bluepylons/Boston/graphics/3DP-LP/3DP-LP-gray-4.JPG

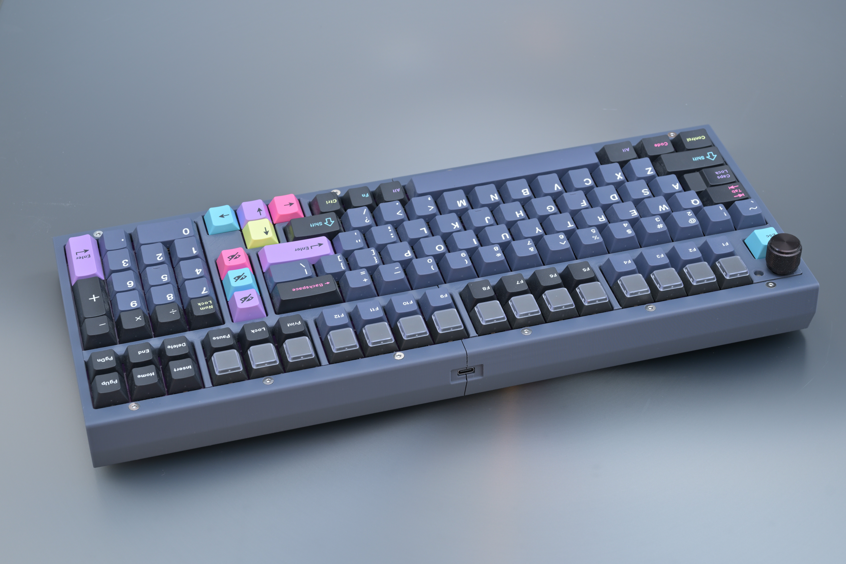
graphics/3DP-LP/3DP-LP-gray-4.JPG
