bluepylons/Boston/graphics/Metal-and-3DP-LP.JPG

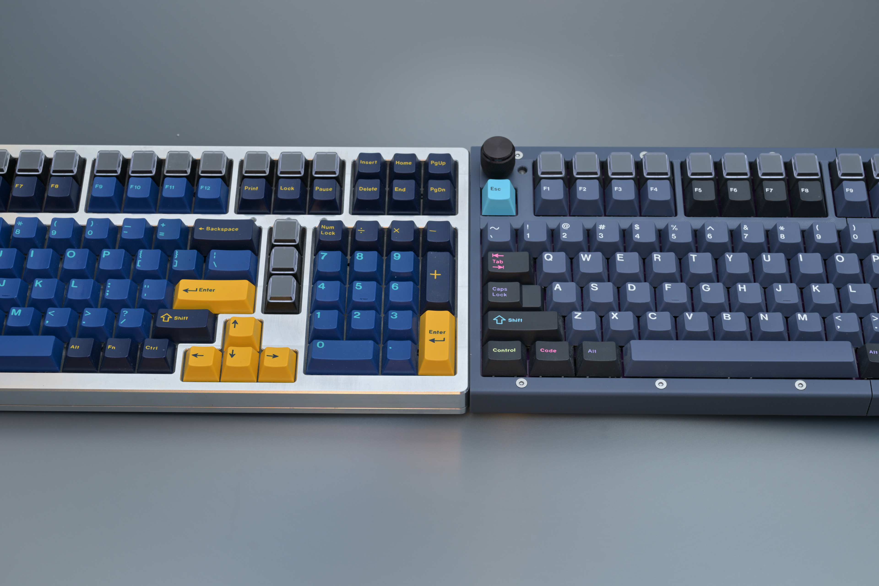
graphics/Metal-and-3DP-LP.JPG
