bluepylons/Boston/graphics/PCB-DB-bottom.png

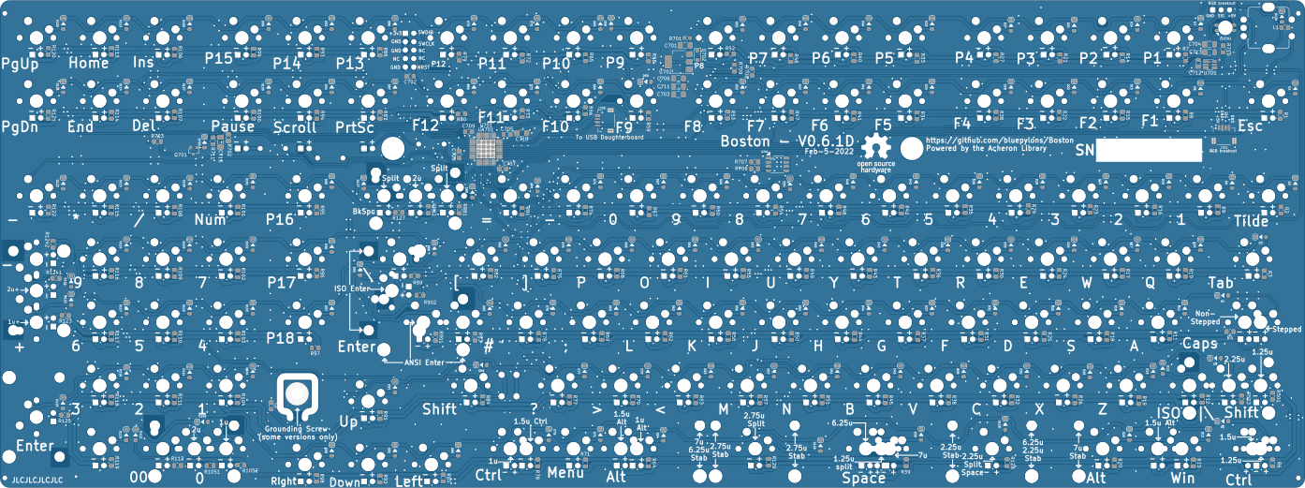
graphics/PCB-DB-bottom.png
