bluepylons/Boston/graphics/PCB-DB-top.png

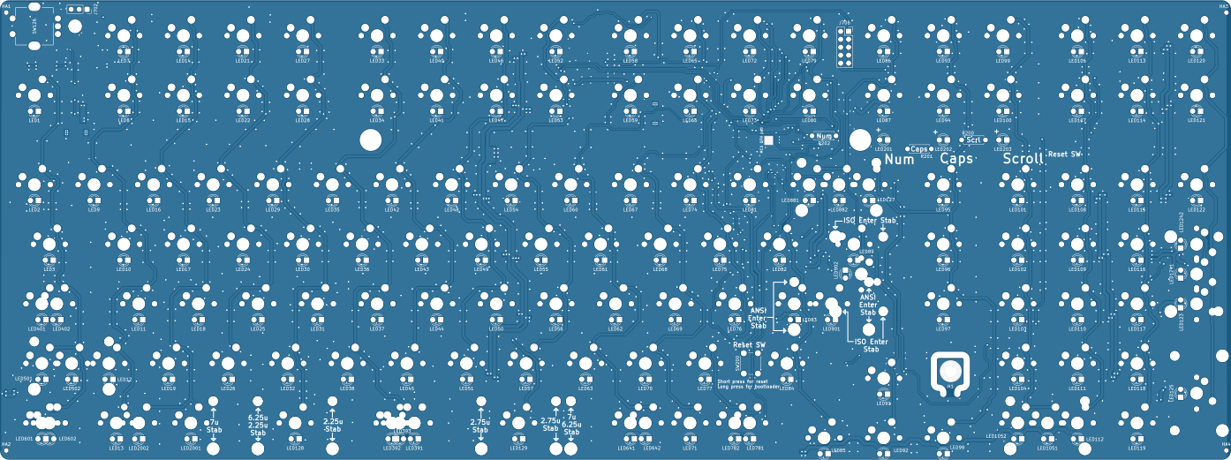
graphics/PCB-DB-top.png
