bluepylons/Boston/graphics/PCB-HS-bottom.png

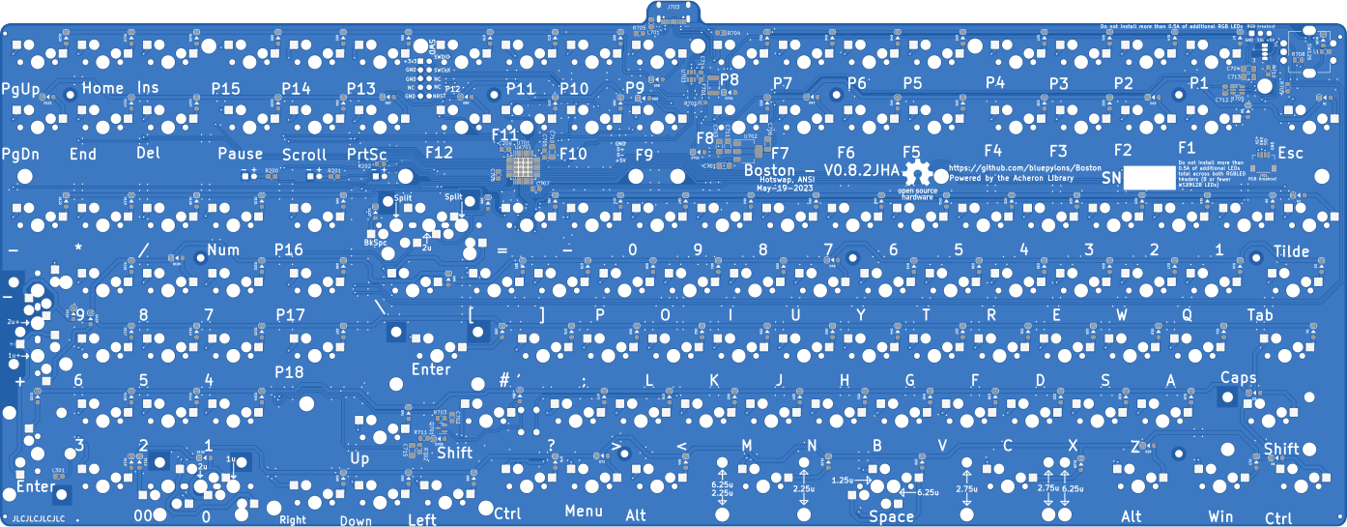
graphics/PCB-HS-bottom.png
