bluepylons/Boston/graphics/PCB-HS-DB-bottom.png

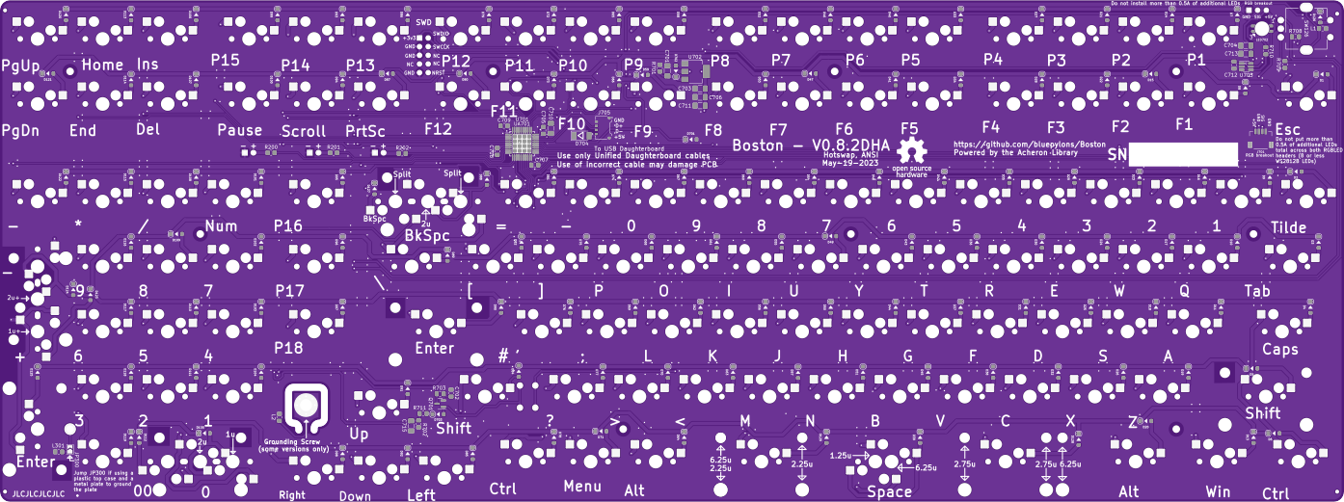
graphics/PCB-HS-DB-bottom.png
