bluepylons/Boston/graphics/PCB-HS-DB-top.png

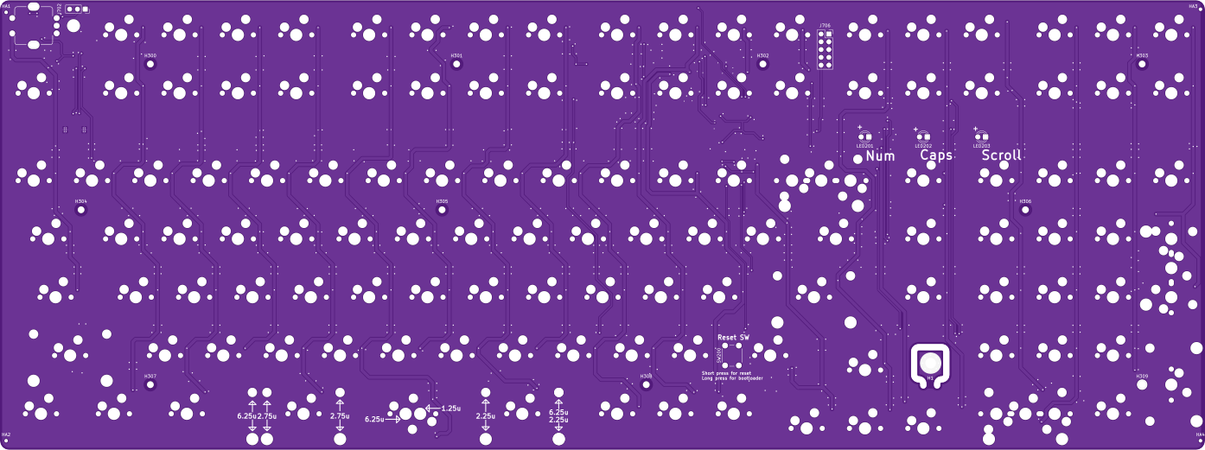
graphics/PCB-HS-DB-top.png
