bluepylons/Boston/graphics/PCB-HS-top.png

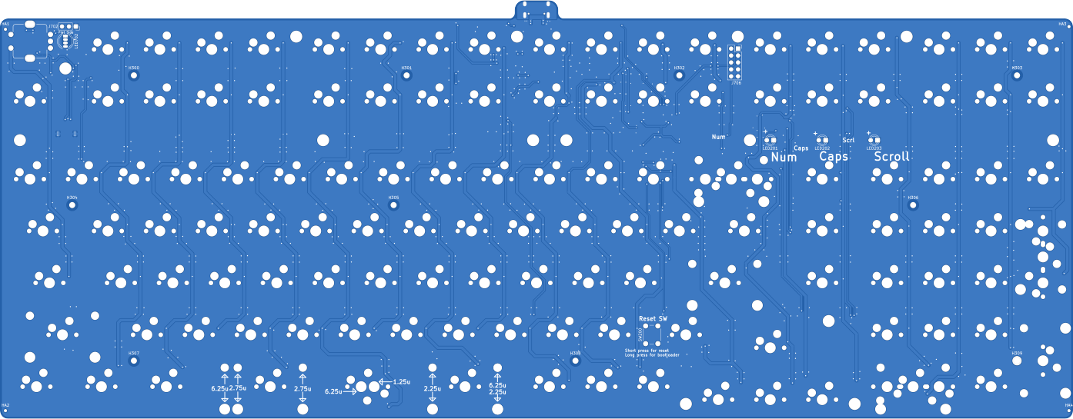
graphics/PCB-HS-top.png
