bluepylons/Boston/graphics/prototype_1_pic.JPG

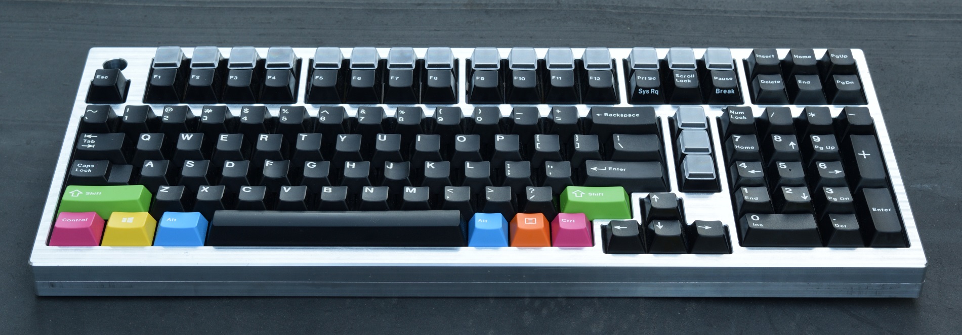
graphics/prototype_1_pic.JPG
