bluepylons/Boston/Boston - Current design/PCB/V0.8.2DHI/Manufacturing files/Elecrow SMT files/BostonV082DHI-Elecrow-files.xlsx

Sheet: PCB Specification
Your PCB Specification
PCB Quantity | 5pcs
Layer | 2layer
PCB Thickness | 1.6mm
Dimensions | 393.5 mm* 147 mm
Castellated Hole | No
PCB Color | Black
Surface Finish | HASL Lead Free
Copper Weight | 1oz
Text Color | White
Different Design | 1

Sheet: BOM
# | Reference | QTY | Value | Package | Manufacturer Part number | Description | SMD | THT | Original | Elecrow PN | Note
1 | C701, C703, C704, C706, C710, C711, C713, C715 | 8 | 10uF 50V X5R or X7R 20% | C1206 | Generic | MLCC Capacitor | 16 |  | N
2 | C702, C705, C707-C709, C712 | 6 | 100nF 50V X5R or X7R 20% | C0805 | Generic | MLCC Capacitor | 12 |  | N
3 | D1-D88, D90-D129, D703 | 129 | 1N4148W | SOD-123 | Generic | Signal Diode | 258 |  | N
4 | D701, D702 | 2 | RB060MM-60TR | SOD-123F | Rohm Semiconductor RB060MM-60TR | Schottky Diode | 4 |  | Y
5 | J705 | 1 | Molex Pico-Ezmate 78171-0004 | Molex Pico-Ezmate 78171-0004 | Molex Pico-Ezmate 78171-0004 | SMT connector | 6 |  | Y
6 | L1, L2, L301 | 3 | 60 ohm @ 100MHz | 0805 | CEC(Shenzhen Zhenhua Fu Elec) PB2012-600/1A0 (LCSC C2983032) | Ferrite bead | 6 |  | Y
7 | LED702 | 1 | SK6812mini-E | 3535_6028_3.2x2.8mm_Round | DONGGUAN OPSCO OPTOELECTRONICS CO., LTD SK6812Mini-E https://cdn-shop.adafruit.com/product-files/4960/4960_SK6812MINI-E_REV02_EN.pdf | SMT addressable RGBLED, reverse mount | 4 |  | Y
8 | Q701 | 1 | DTC123JKAT146 | SOT-23-3 | Rohm Semiconductor DTC123JKAT146 | Transistor | 3 |  | Y
9 | R200-R202 | 3 | 1K 5% | R0805 | Generic | 1K resistor | 6 |  | N
10 | R701 | 1 | 100K 5% | R0805 | Generic | 100K resistor | 2 |  | N
11 | R702 | 1 | 1M 1% | R0805 | Generic | 1M 1% resistor | 2 |  | N
12 | R708, R709 | 2 | 10K 5% | R0805 | Generic | 10K resistor | 4 |  | N
13 | R703, R710 | 2 | 100 5% | R0805 | Generic | 100 resistor | 4 |  | N
14 | R711 | 1 | 330K 1% | R0805 | Generic | 330K 1% resistor | 2 |  | N
15 | SW1-SW38,SW39-1,SW39-2,SW40-SW87,SW88-1,SW88-2,SW90-SW104,SW105-1,SW105-2,SW106-SW123,SW124-1,SW124-2,SW125-SW129 | 132 |  | Custom | Kailh CPG151101S11 | Keyboard switch socket | 264 |  | Y | CRP13070O | Black
16 | SW200 | 1 | SW_Push | Tact 6x6 5mm tall THT | Generic (e.g. Hongyuan Precision 1TS005A-2600-5001) | Tact switch |  | 4 | N |  | Solder to top side, not bottom!
17 | U701 | 1 | STM32F072CBx | LQFP-48 or QFN-48 | Any of the following: ST STM32F072CBU6 ST STM32F072CBU6TR ST STM32F072CBU7 ST STM32F072CBU7TR ST STM32F072CBT6 ST STM32F072CBT6TR ST STM32F072CBT7 ST STM32F072CBT7TR | Microcontroller | 49 |  | Y
18 | U702 | 1 | 3.3V LDO | SOT-223 | Any of the following: TI TLV1117LV33DCYR Diodes Inc AZ1117IH-3.3TRG1 | 3.3V LDO | 4 |  | Y
19 | U705 | 1 | 74LVC1T45 | SOT23-6 | Any of the following: TI SN74LVC1T45DBVR TI SN74LVC1T45DBVT Diodes Inc 74LVC1T45W6-7 | Level shifter | 6 |  | Y
20 | D704 | 1 | PMEG6030EVPX | SOD-128 | Nexperia PMEG6030EVPX | Schottky Diode | 2 |  | Y
 |  |  |  |  |  | Total | 638 | 4

Sheet: Position
Designator | Footprint | Center-X(mm) | Center-Y(mm) | Layer | Rotation
C701 | C_1206_3216Metric_Pad1.42x1.75mm_HandSolder | 253.1 | -48.725 | bottom | 90
C702 | C_0805_2012Metric_Pad1.15x1.40mm_HandSolder | 316.4 | -143.125 | bottom | 90
C703 | C_1206_3216Metric_Pad1.42x1.75mm_HandSolder | 243.5 | -53.925 | bottom | 0
C704 | C_1206_3216Metric_Pad1.42x1.75mm_HandSolder | 83.75 | -41.325 | bottom | 0
C705 | C_0805_2012Metric_Pad1.15x1.40mm_HandSolder | 289.4 | -66.164069 | bottom | -90
C706 | C_1206_3216Metric_Pad1.42x1.75mm_HandSolder | 243.5 | -56.425 | bottom | 0
C707 | C_0805_2012Metric_Pad1.15x1.40mm_HandSolder | 291.9 | -76.325 | bottom | 0
C708 | C_0805_2012Metric_Pad1.15x1.40mm_HandSolder | 302.9 | -72.325 | bottom | 90
C709 | C_0805_2012Metric_Pad1.15x1.40mm_HandSolder | 300.890625 | -64.821875 | bottom | 180
C710 | C_1206_3216Metric_Pad1.42x1.75mm_HandSolder | 287.2 | -65.568756 | bottom | -90
C711 | C_1206_3216Metric_Pad1.42x1.75mm_HandSolder | 243.5 | -58.925 | bottom | 0
C712 | C_0805_2012Metric_Pad1.15x1.40mm_HandSolder | 87.2 | -47.025 | bottom | -90
C713 | C_1206_3216Metric_Pad1.42x1.75mm_HandSolder | 83.725 | -43.725 | bottom | 0
C715 | C_1206_3216Metric_Pad1.42x1.75mm_HandSolder | 328.1 | -152.725 | bottom | -90
D1 | D_SOD-123 | 61.5 | -49.725 | bottom | 180
D2 | D_SOD-123 | 69.1 | -78.225 | bottom | 180
D3 | D_SOD-123 | 62.428125 | -98.90625 | bottom | -90
D4 | D_SOD-123 | 64.809375 | -117.95625 | bottom | -90
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
SW97 | MX100H | 356.5125 | -125.1 | bottom | 180
SW98 | MX100H | 356.5125 | -167.9625 | bottom | 180
SW99 | MX100H | 375.5625 | -39.375 | bottom | 180
SW100 | MX100H | 375.5625 | -58.425 | bottom | 180
SW101 | MX100H | 380.325 | -87 | bottom | 180
SW102 | MX100H | 380.325 | -106.05 | bottom | 180
SW103 | MX100H | 380.325 | -125.1 | bottom | 180
SW104 | MX100H | 380.325 | -144.15 | bottom | 180
SW105-1 | MX200H | 389.85 | -163.2 | bottom | 180
SW105-2 | MX100H | 380.325 | -163.2 | bottom | 0
SW106 | MX100H | 399.375 | -39.375 | bottom | 180
SW107 | MX100H | 399.375 | -58.425 | bottom | 180
SW108 | MX100H | 399.375 | -87 | bottom | 180
SW109 | MX100H | 399.375 | -106.05 | bottom | 180
SW110 | MX100H | 399.375 | -125.1 | bottom | 180
SW111 | MX100H | 399.375 | -144.15 | bottom | 180
SW112 | MX100H | 399.375 | -163.2 | bottom | 0
SW113 | MX100H | 418.425 | -39.375 | bottom | 180
SW114 | MX100H | 418.425 | -58.425 | bottom | 180
SW115 | MX100H | 418.425 | -87 | bottom | 180
SW116 | MX100H | 418.425 | -106.05 | bottom | 180
SW117 | MX100H | 418.425 | -125.1 | bottom | 180
SW118 | MX100H | 418.425 | -144.15 | bottom | 180
SW119 | MX100H | 418.425 | -163.2 | bottom | 180
SW120 | MX100H | 437.475 | -39.375 | bottom | 180
SW121 | MX100H | 437.475 | -58.425 | bottom | 180
SW122 | MX100H | 437.475 | -87 | bottom | 180
SW123 | MX100H | 437.475 | -125.1 | bottom | -90
SW124-1 | MX200H | 437.475 | -115.575 | bottom | 90
SW124-2 | MX100H | 437.475 | -106.05 | bottom | -90
SW125 | MX200HR | 437.475 | -153.675 | bottom | 90
SW126 | ALPS_EC11E | 66 | -36.375 | bottom | -90
SW127 | MX100H | 332.7 | -87 | bottom | 0
SW128 | MX275H | 154.10625 | -163.2 | bottom | 180
SW129 | MX225H | 225.54375 | -163.2 | bottom | 180
U701 | LQFP-48_7x7mm_P0.5mm | 295.650625 | -70.066875 | bottom | 180
U702 | SOT-223-3_TabPin2 | 244.8 | -48.925 | bottom | 180
U705 | SOT-23-6_Handsoldering | 83.62125 | -47.47125 | bottom | 180
