bluepylons/Boston/graphics/Assembly-guide-3DP/Parts-FR4-rubber-feet-holder.jpg

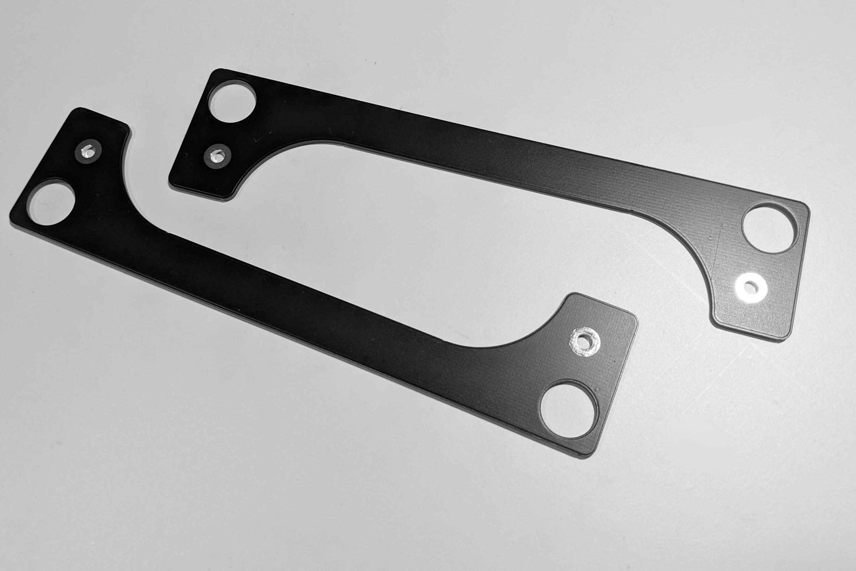
graphics/Assembly-guide-3DP/Parts-FR4-rubber-feet-holder.jpg
