bluepylons/Boston/graphics/Assembly-guide-3DP/Parts-rubber-feet.jpg

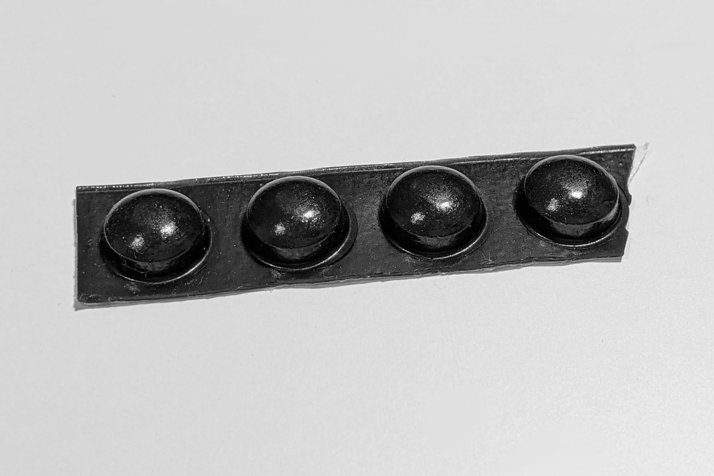
graphics/Assembly-guide-3DP/Parts-rubber-feet.jpg
