bluepylons/Boston/Experimental designs/Lower profile 3DP/Right-key-separator-revised.stp

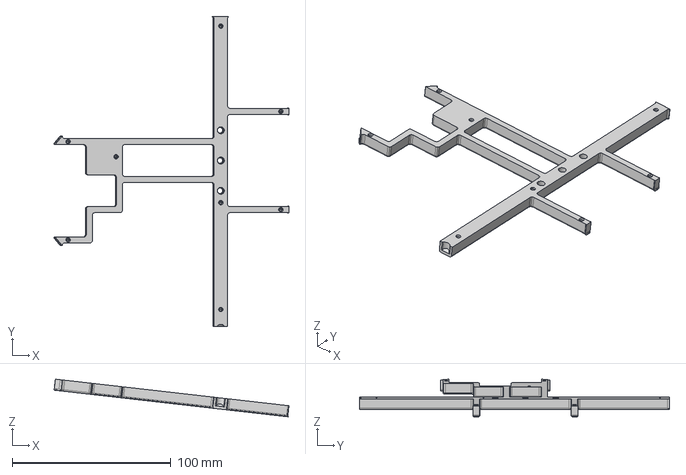
[picture p52: CAD file, 2026-01-18]
Experimental designs/Lower profile 3DP/Right-key-separator-revised.stp
148.0 x 195.4 x 23.8 mm
