bluepylons/Boston/Boston - Current design/3D printed version/STLs/RGBLED-LED-spacer.stl

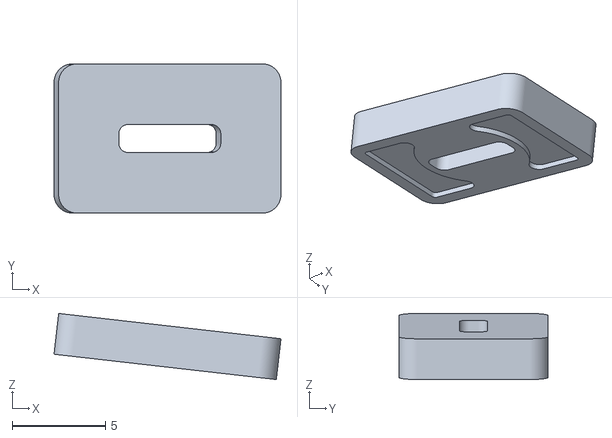
[picture p53: CAD file, 2023-04-24]
Boston - Current design/3D printed version/STLs/RGBLED-LED-spacer.stl
12.2 x 8.00 x 3.54
