bluepylons/Boston/Boston - Current design/CNC version/Case/STEP/Boston-top.stp

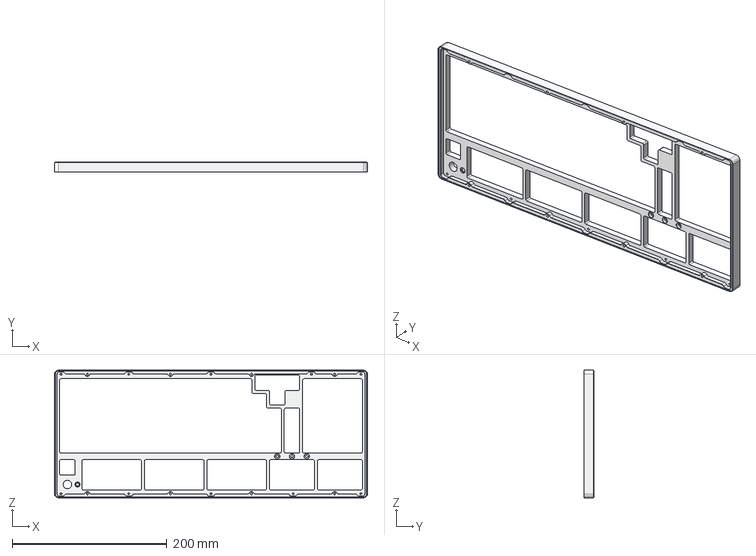
[picture p54: CAD file, 2023-04-24]
Boston - Current design/CNC version/Case/STEP/Boston-top.stp
405.0 x 13.5 x 165.0 mm
