bluepylons/Boston/Experimental designs/Lower profile 3DP/Lower-profile-right-half.stp

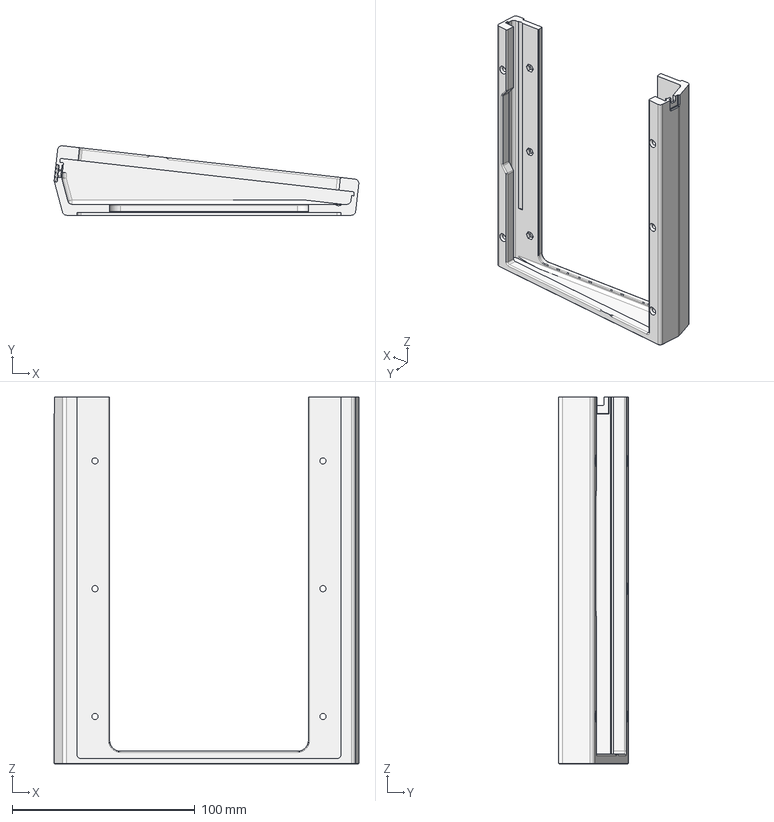
[picture p55: CAD file, 2026-01-18]
Experimental designs/Lower profile 3DP/Lower-profile-right-half.stp
166.9 x 38.1 x 201.0 mm
