bluepylons/Boston/Boston - Current design/3D printed version/STLs/Right-half.stl

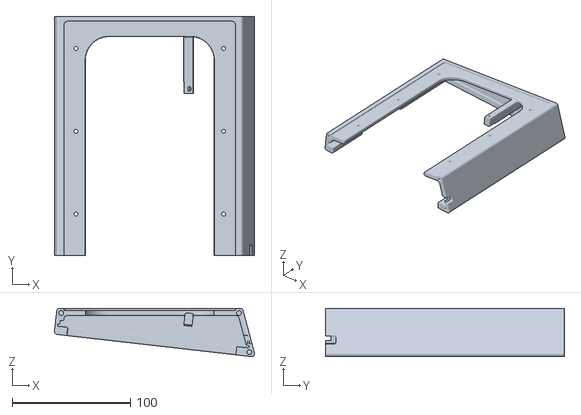
[picture p57: CAD file, 2023-04-24]
Boston - Current design/3D printed version/STLs/Right-half.stl
169.3 x 202.0 x 40.8
