bluepylons/Boston/Boston - Current design/3D printed version/STLs/3mm-LED-spacer.stl

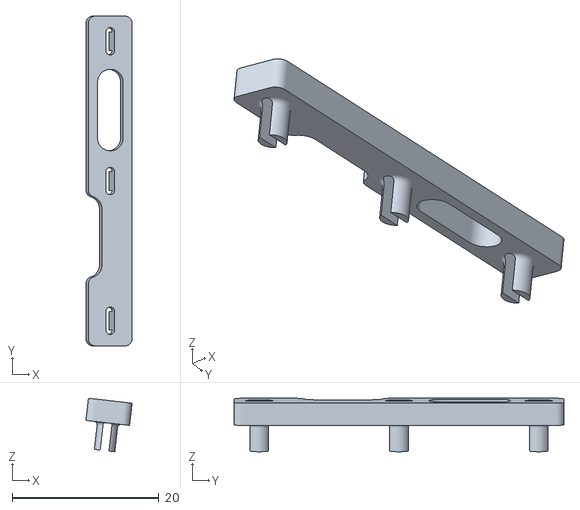
[picture p58: CAD file, 2023-04-24]
Boston - Current design/3D printed version/STLs/3mm-LED-spacer.stl
6.31 x 45.0 x 7.30
