bluepylons/Boston/Boston - Current design/3D printed version/Bottom (without reset hole)/Artwork files (courtesy OpenStreetMap)/boston-streets-8.png

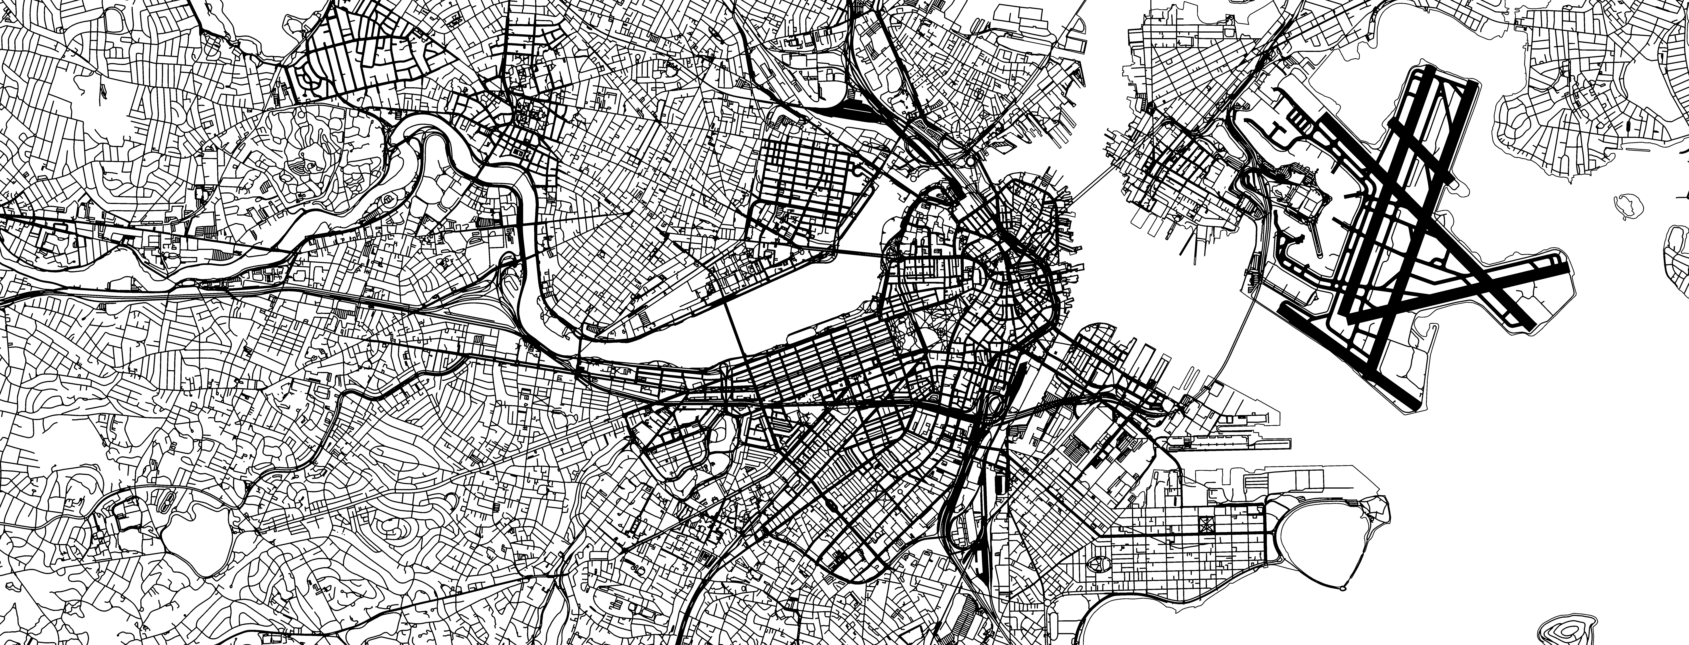
Boston - Current design/3D printed version/Bottom (without reset hole)/Artwork files (courtesy OpenStreetMap)/boston-streets-8.png
