bluepylons/Boston/Boston - Current design/CNC version/Case/Manufacturing drawings/Boston-bottom-alternate-AS-MACHINED-milling-instructions.png

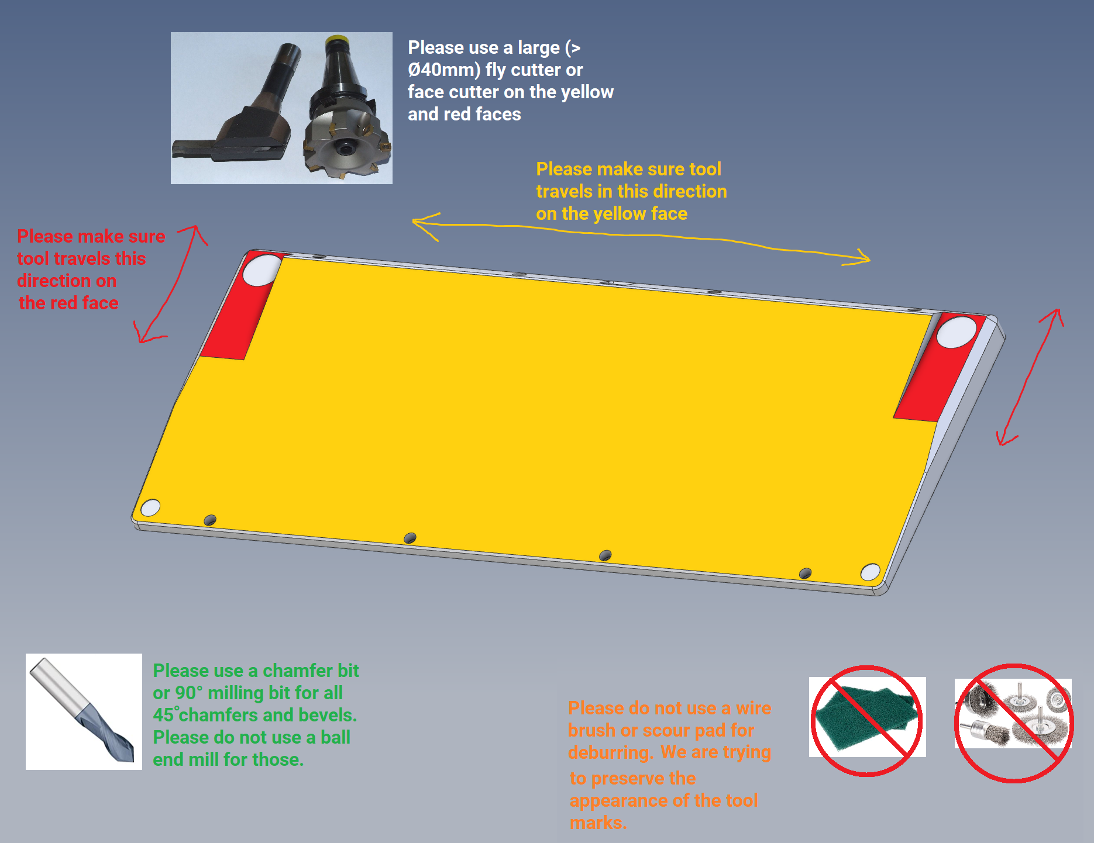
Boston - Current design/CNC version/Case/Manufacturing drawings/Boston-bottom-alternate-AS-MACHINED-milling-instructions.png
