bluepylons/Boston/Boston - Current design/CNC version/Case/Manufacturing drawings/Boston-bottom-AS-MACHINED-milling-instructions.png

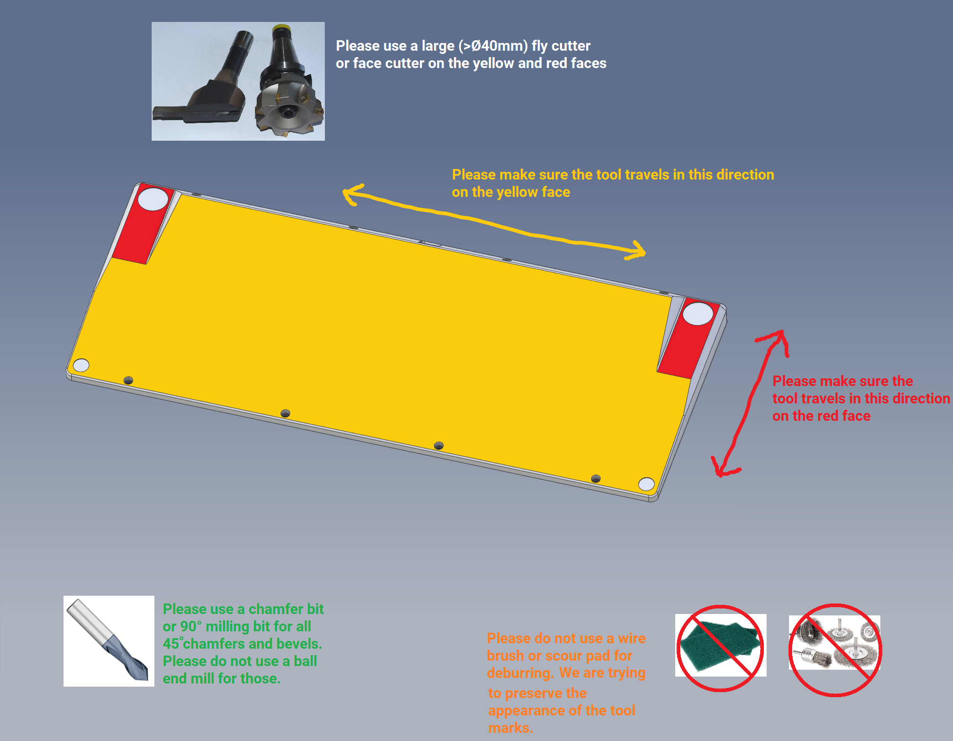
Boston - Current design/CNC version/Case/Manufacturing drawings/Boston-bottom-AS-MACHINED-milling-instructions.png
