bluepylons/Boston/Boston - Current design/PCB/V0.8.2DHA/Manufacturing files/Elecrow SMT files/SW200-instructions.png

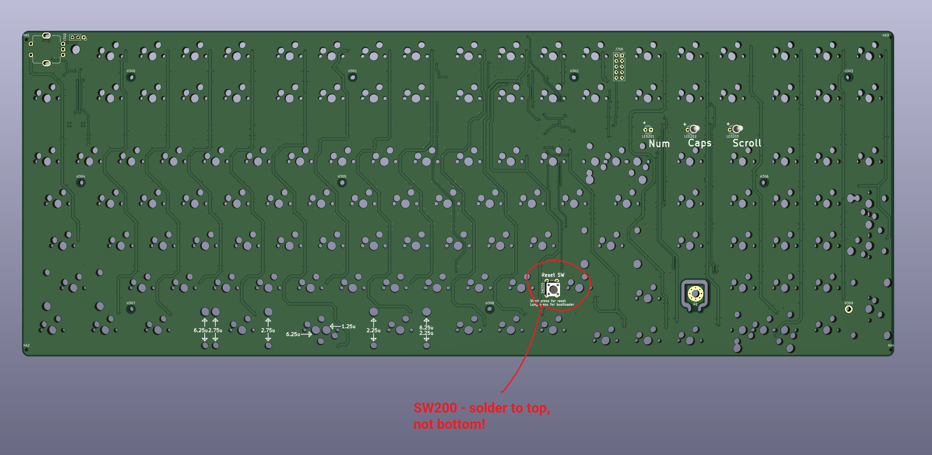
Boston - Current design/PCB/V0.8.2DHA/Manufacturing files/Elecrow SMT files/SW200-instructions.png
