bluepylons/Boston/Boston - Current design/PCB/V0.8.2DHI/Manufacturing files/Elecrow SMT files/SW200.png

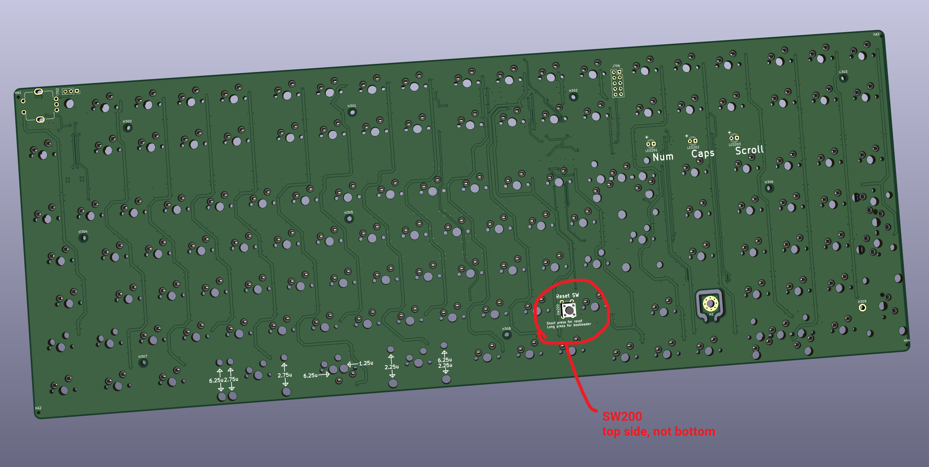
Boston - Current design/PCB/V0.8.2DHI/Manufacturing files/Elecrow SMT files/SW200.png
