bluepylons/Boston/Boston - Current design/PCB/V0.8.2JHA/Manufacturing files/Elecrow SMT files/SW200+LED702-instructions.png

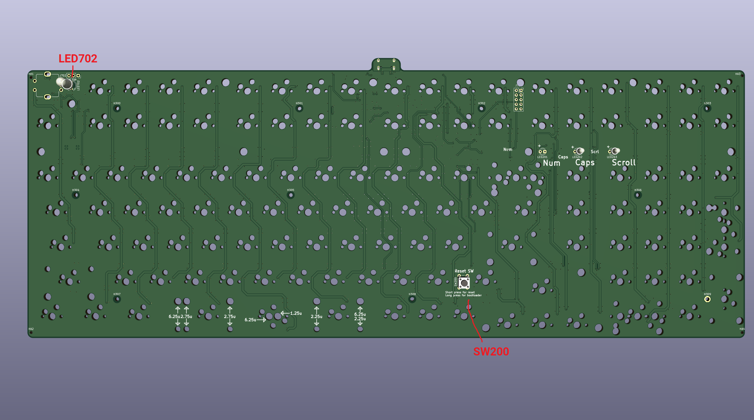
Boston - Current design/PCB/V0.8.2JHA/Manufacturing files/Elecrow SMT files/SW200+LED702-instructions.png
