bluepylons/Boston/Boston - Current design/PCB/V0.8D/Manufacturing files/Elecrow SMT files/SW200-instructions.png

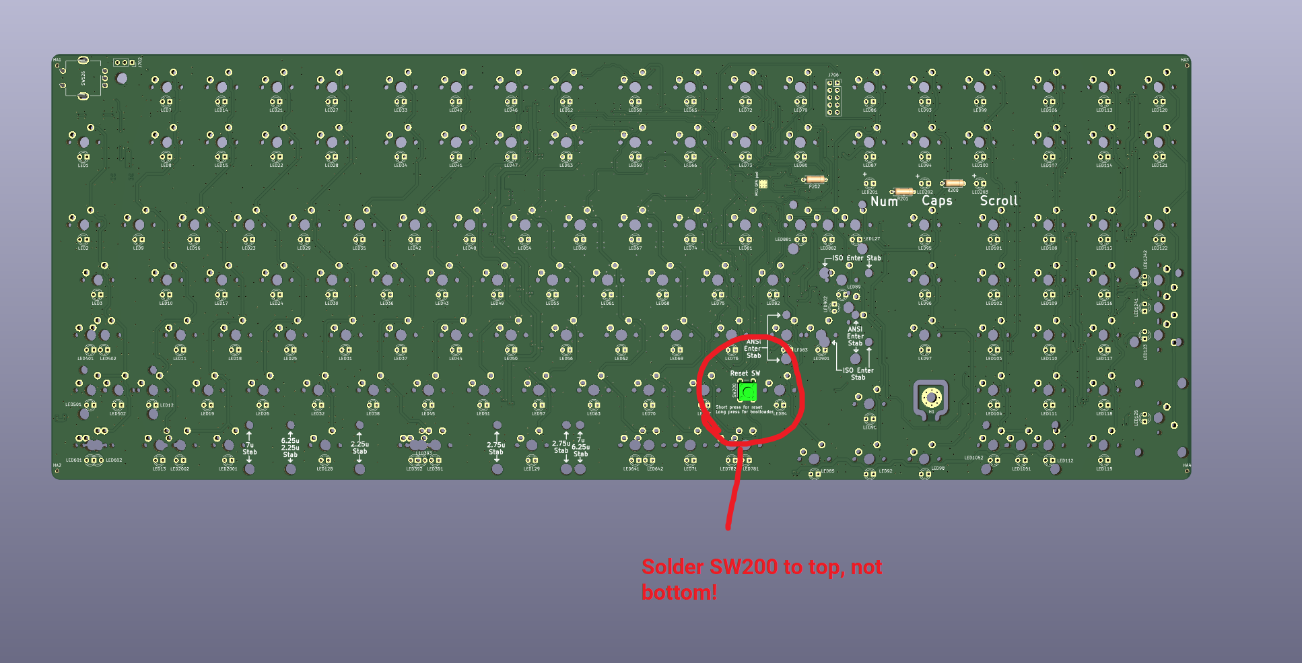
Boston - Current design/PCB/V0.8D/Manufacturing files/Elecrow SMT files/SW200-instructions.png
