bluepylons/Boston/Boston - Current design/PCB/V0.8J/Manufacturing files/Elecrow SMT files/SW200+LED702-instructions.png

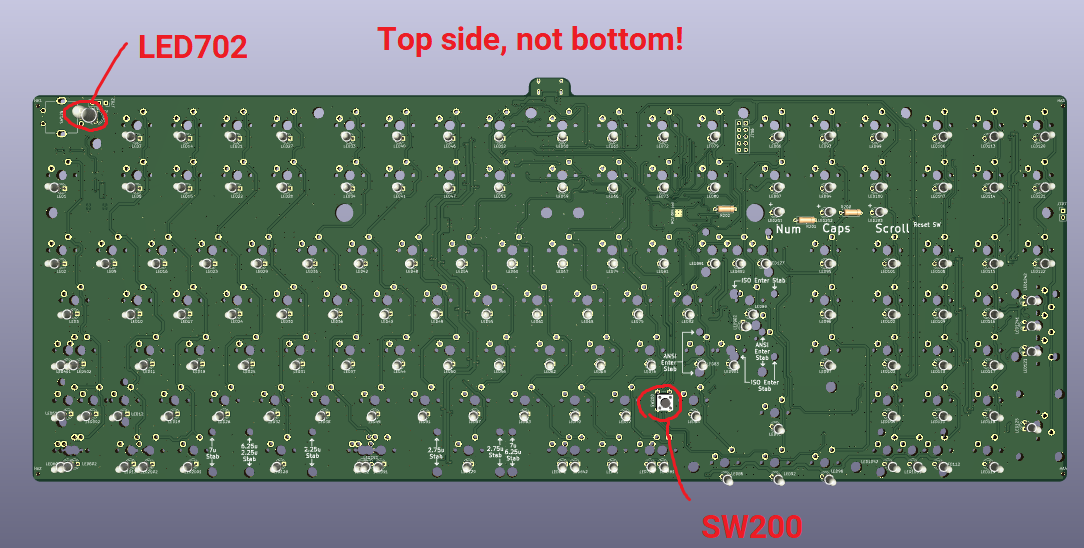
Boston - Current design/PCB/V0.8J/Manufacturing files/Elecrow SMT files/SW200+LED702-instructions.png
