bluepylons/Boston/graphics/3DP-LP/3DP-LP-half-assembled2.JPG

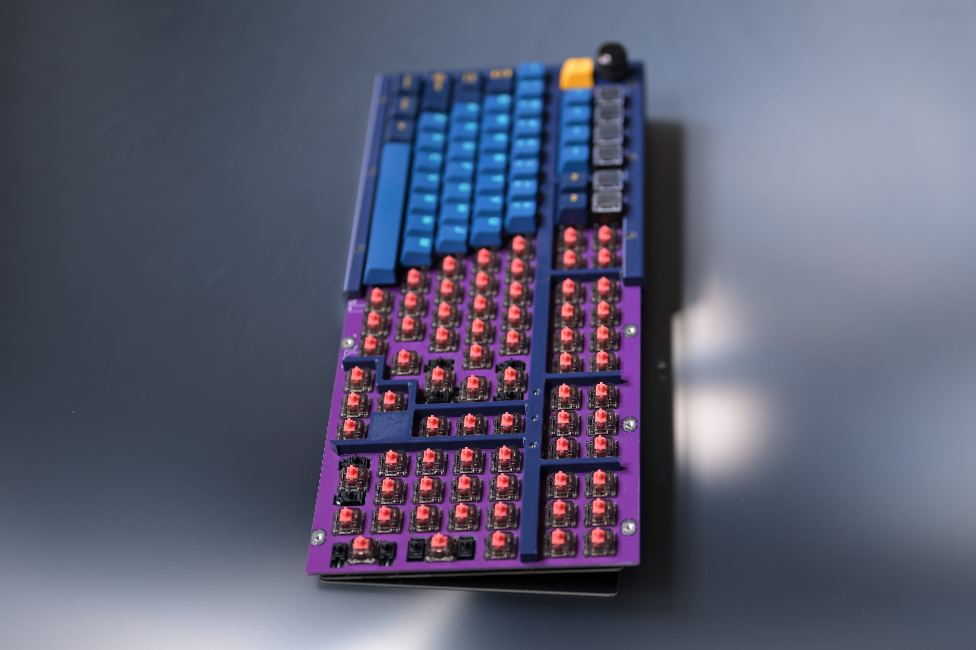
graphics/3DP-LP/3DP-LP-half-assembled2.JPG
