bluepylons/Boston/graphics/3DP-LP/3DP-LP-half-assembled.JPG

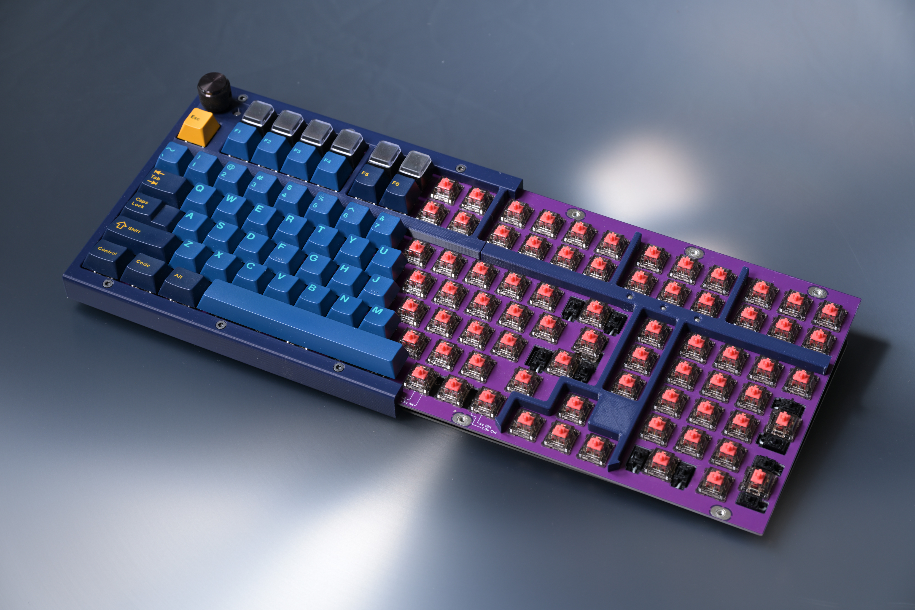
graphics/3DP-LP/3DP-LP-half-assembled.JPG
