bluepylons/Boston/graphics/Assembly-guide-3DP/PCB-LED-polarity.jpg

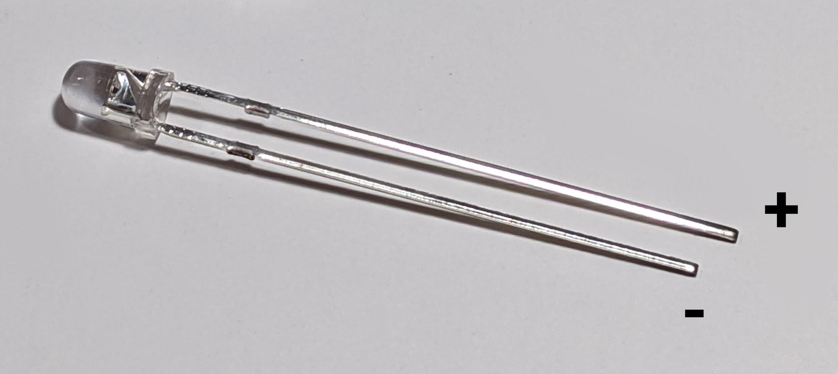
graphics/Assembly-guide-3DP/PCB-LED-polarity.jpg
