bluepylons/Boston/Boston - Current design/PCB/Older PCB revisions/V0.8.1JHA/Boston-keyboard-V081JHA.pdf

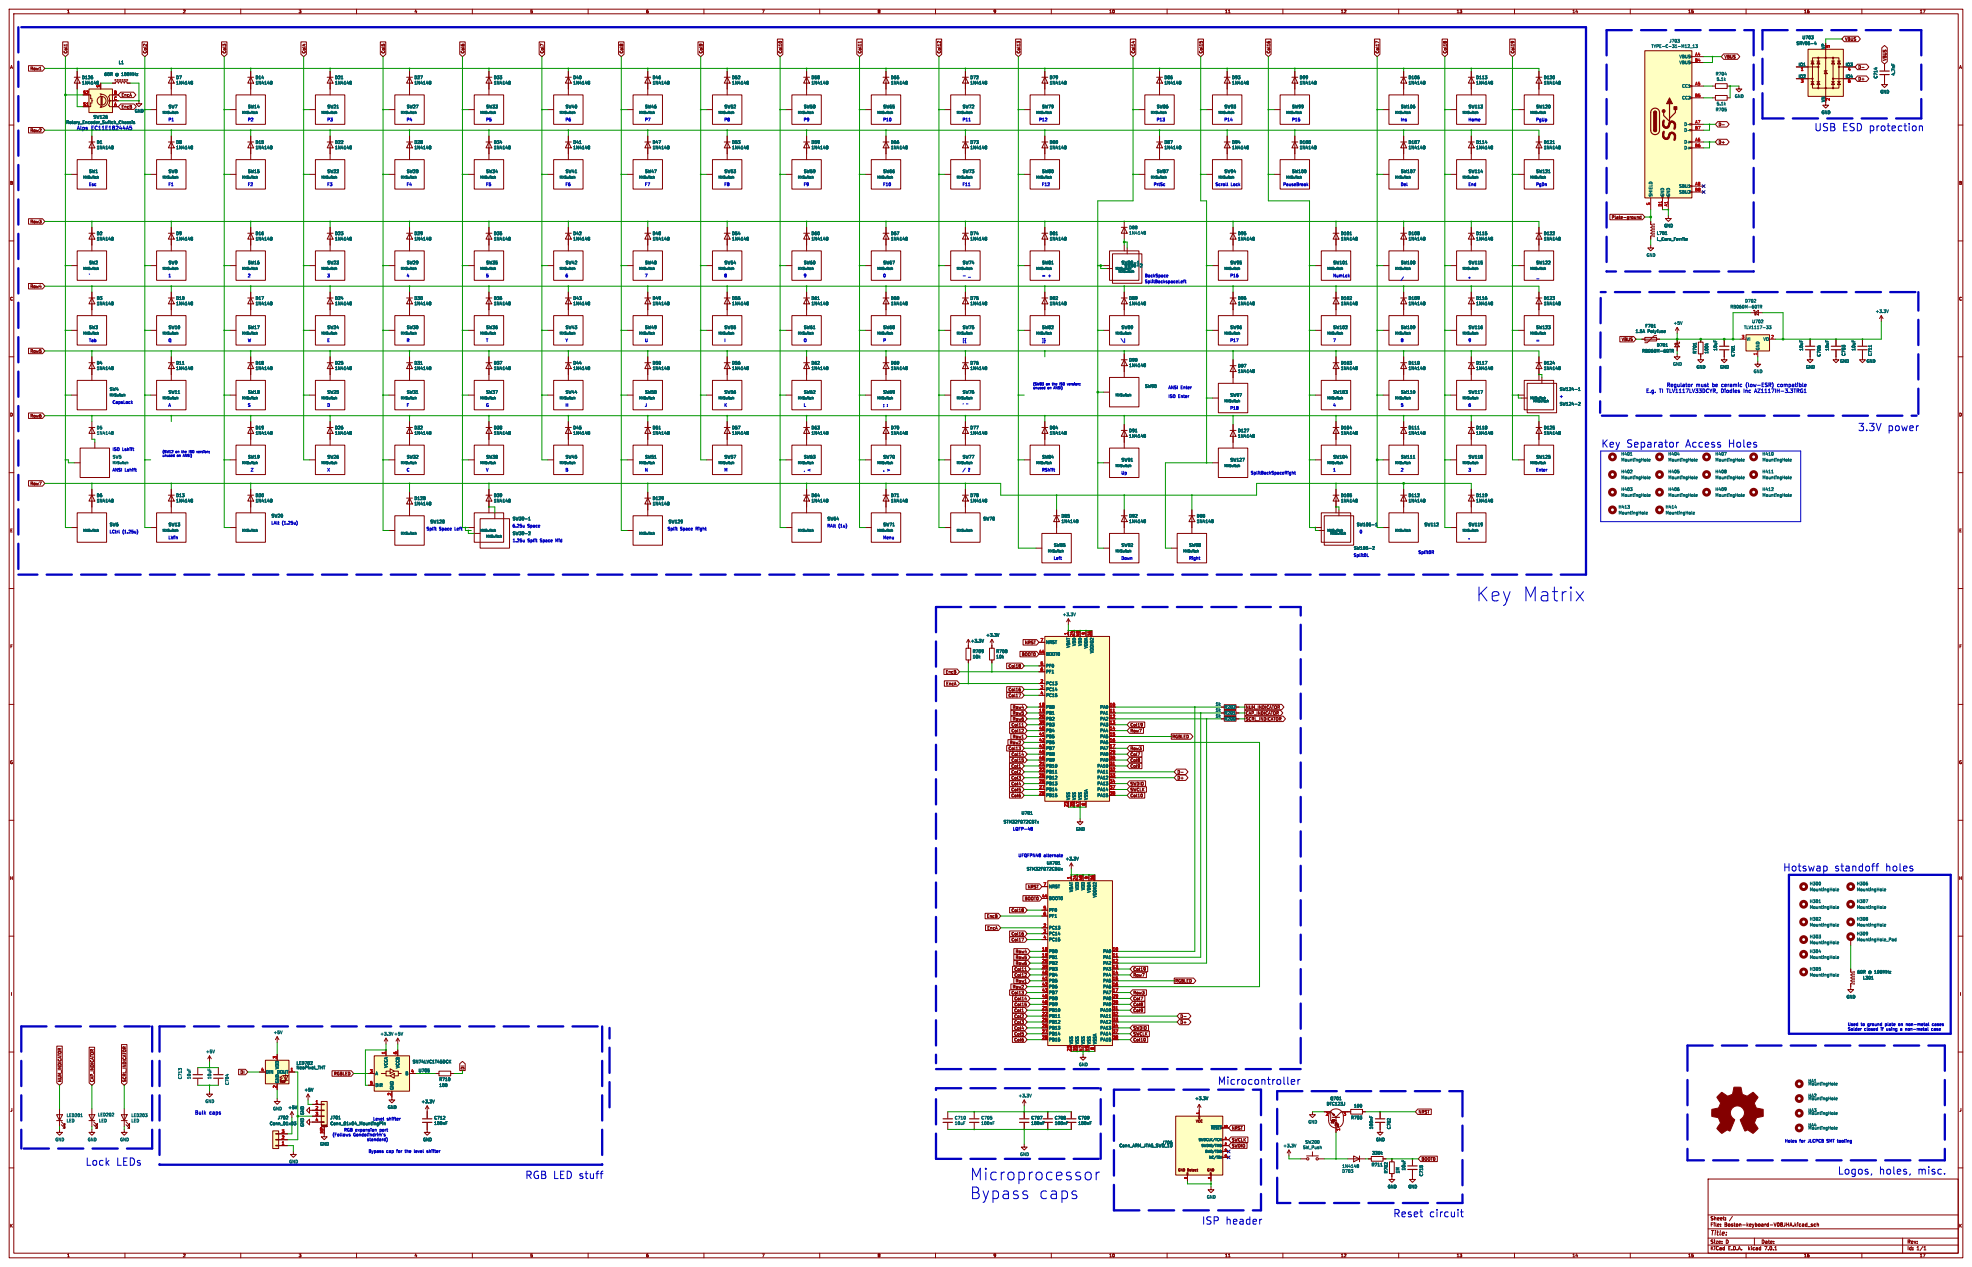
[picture p190: page 1]

Key Separator Access Holes

Holes for JLCPCB SMT tooling

Bypass cap for the level shifter
