bluepylons/Boston/Boston - Current design/3D printed version/Bumpon holders/bumpon-holders.kicad_sch

## KiCad design Boston - Current design/3D printed version/Bumpon holders/bumpon-holders.kicad_sch (2023-04-24)

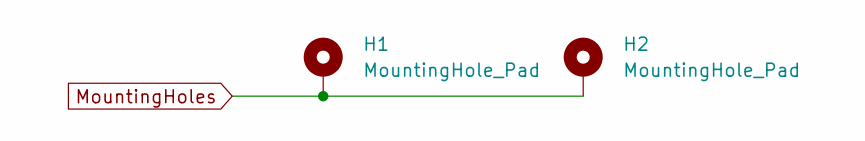
[picture p191: schematic bumpon-holders.kicad_sch]

Parts:
H1, H2: MountingHole_Pad; MountingHole_3.2mm_M3_Pad

Connections:
MountingHoles: H1.1, H2.1
