bluepylons/Boston/Boston - Current design/CNC version/Daughterboard holder (C3 or C4 DB only)/Daughterboard-holder.kicad_sch

## KiCad design Boston - Current design/CNC version/Daughterboard holder (C3 or C4 DB only)/Daughterboard-holder.kicad_sch (2023-04-24)

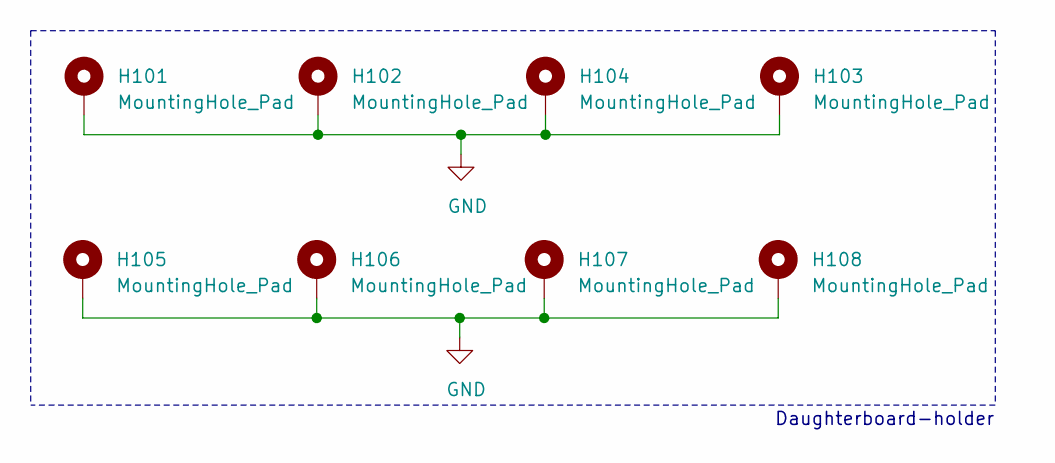
[picture p192: schematic Daughterboard-holder.kicad_sch]

Parts:
H101: MountingHole_Pad; MountingHole_3.2mm_M3_Pad
H102, H103, H104: MountingHole_Pad; MountingHole_3.5mm_Pad
H105, H106, H107, H108: MountingHole_Pad; MountingHole_4mm_Pad

Connections:
GND: H101.1, H102.1, H103.1, H104.1, H105.1, H106.1, H107.1, H108.1

Notes on the sheet:
Daughterboard-holder
