bluepylons/Boston/Boston - Current design/3D printed version/Plate/Plate-hotswap-ANSI/3DP-FR4-hotswap-plate-ANSI.kicad_sch

## KiCad design Boston - Current design/3D printed version/Plate/Plate-hotswap-ANSI/3DP-FR4-hotswap-plate-ANSI.kicad_sch (2023-04-24)

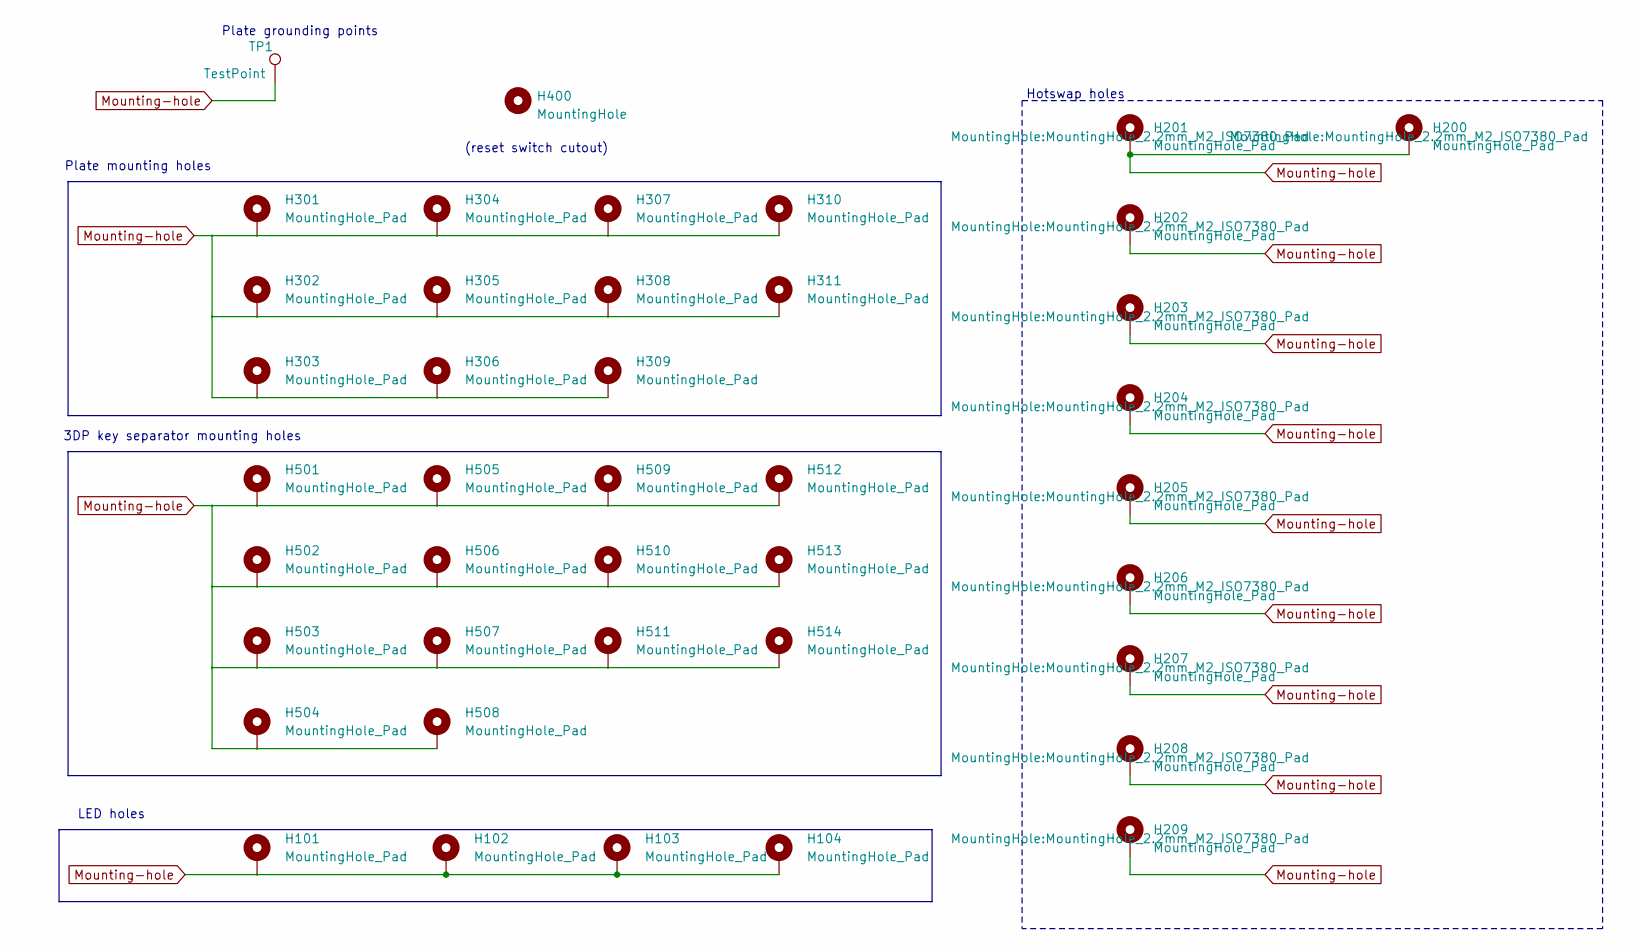
[picture p193: schematic 3DP-FR4-hotswap-plate-ANSI.kicad_sch]

Parts:
H101, H501, H502, H503, H504, H505, H506, H507, H508, H509, H510, H511, H512, H514: MountingHole_Pad; MountingHole_2.2mm_M2_Pad
H102, H103, H104, H513: MountingHole_Pad; MountingHole_5.3mm_M5_DIN965_Pad
H200, H201, H202, H203, H204, H205, H206, H207, H208, H209: MountingHole_Pad; MountingHole_2.2mm_M2_ISO7380_Pad
H301, H302, H303, H304, H305, H306, H307, H308, H309, H310, H311: MountingHole_Pad; PEM-KF2-M3-ET_(solder-in)
H400: MountingHole; 6x6-Tact-switch-opening-enlarged
TP1: TestPoint; Pad-4x10mm

Connections:
Mounting-hole: H101.1, H102.1, H103.1, H104.1, H200.1, H201.1, H202.1, H203.1, H204.1, H205.1, H206.1, H207.1, H208.1, H209.1, H301.1, H302.1, H303.1, H304.1, H305.1, H306.1, H307.1, H308.1, H309.1, H310.1, H311.1, H501.1, H502.1, H503.1, H504.1, H505.1, H506.1, H507.1, H508.1, H509.1, H510.1, H511.1, H512.1, H513.1, H514.1, TP1.1

Notes on the sheet:
Hotswap holes
Plate mounting holes
LED holes
3DP key separator mounting holes
(reset switch cutout)
Plate grounding points
