bluepylons/Boston/Boston - Current design/3D printed version/Plate/Plate-soldered-universal-3DP/3DP-FR4-plate-top-reset-cutout.kicad_sch

## KiCad design Boston - Current design/3D printed version/Plate/Plate-soldered-universal-3DP/3DP-FR4-plate-top-reset-cutout.kicad_sch (2023-04-24)

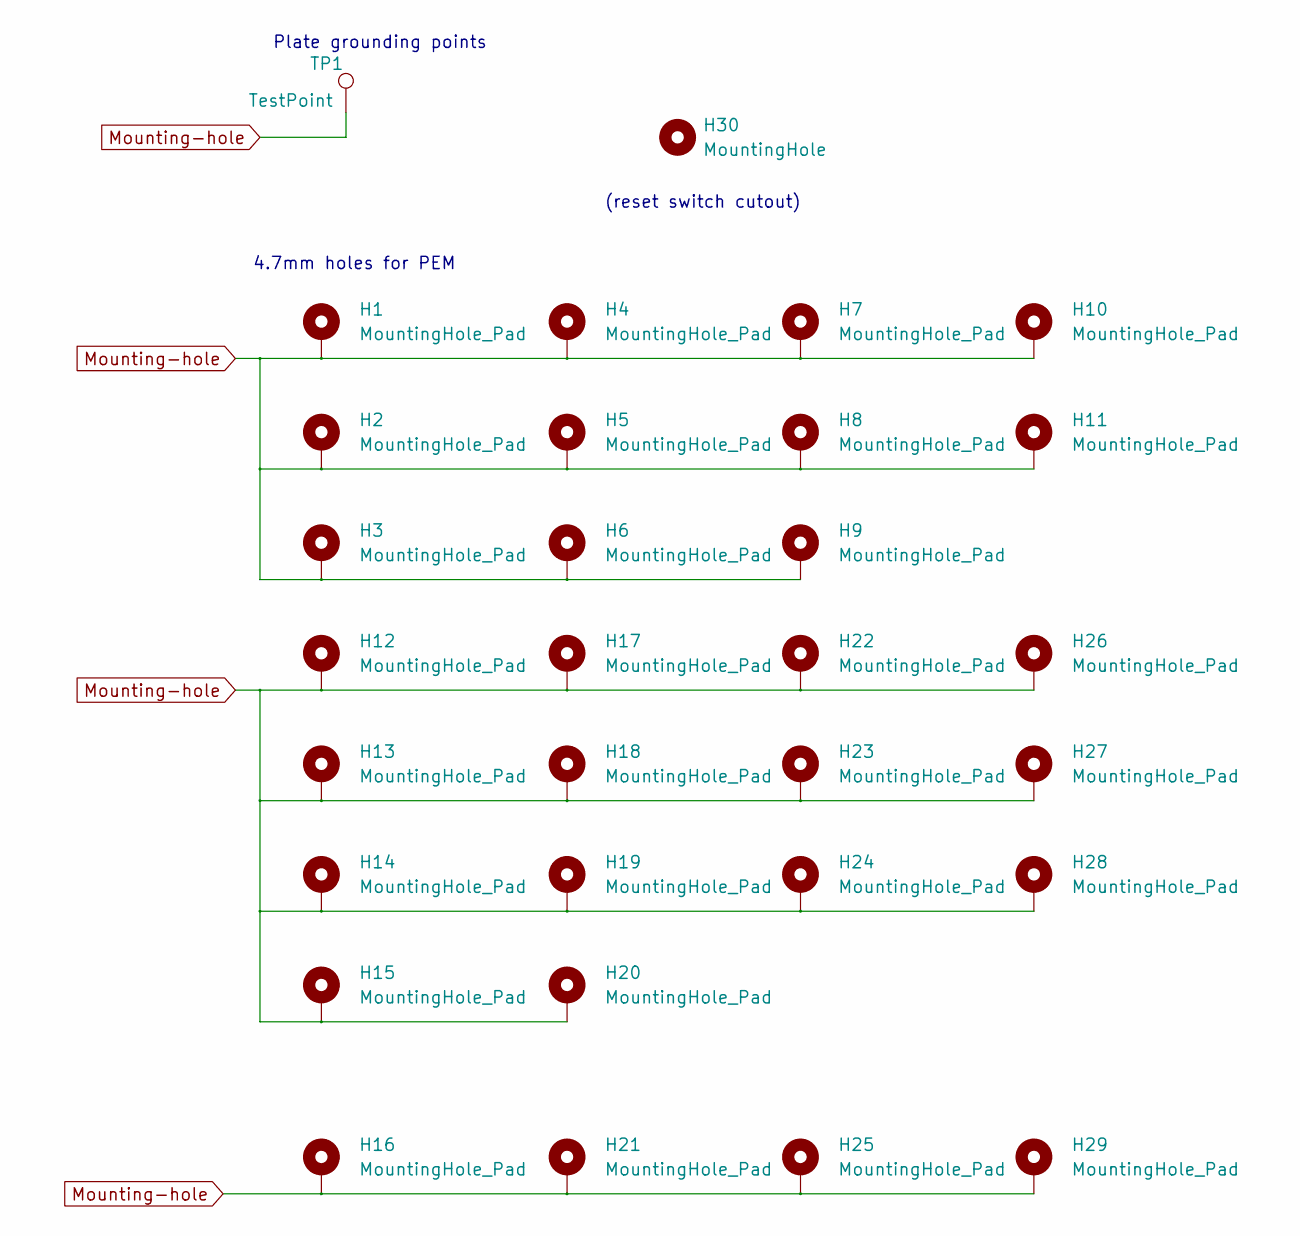
[picture p194: schematic 3DP-FR4-plate-top-reset-cutout.kicad_sch]

Parts:
H1, H2, H3, H4, H5, H6, H7, H8, H9, H10, H11: MountingHole_Pad; PEM-KF2-M3-ET_(solder-in)
H12, H13, H14, H15, H16, H17, H18, H19, H20, H21, H22, H23, H24, H25: MountingHole_Pad; MountingHole_2.2mm_M2_Pad
H26, H27, H28, H29: MountingHole_Pad; MountingHole_5.3mm_M5_DIN965_Pad
H30: MountingHole; 6x6-Tact-switch-opening-enlarged
TP1: TestPoint; Pad-4x10mm

Connections:
Mounting-hole: H1.1, H2.1, H3.1, H4.1, H5.1, H6.1, H7.1, H8.1, H9.1, H10.1, H11.1, H12.1, H13.1, H14.1, H15.1, H16.1, H17.1, H18.1, H19.1, H20.1, H21.1, H22.1, H23.1, H24.1, H25.1, H26.1, H27.1, H28.1, H29.1, TP1.1

Notes on the sheet:
4.7mm holes for PEM
(reset switch cutout)
Plate grounding points
