bluepylons/Boston/Boston - Current design/CNC version/Plate/Hotswap-ISO/KiCAD files/FR4-hotswap-ISO-plate.kicad_sch

## KiCad design Boston - Current design/CNC version/Plate/Hotswap-ISO/KiCAD files/FR4-hotswap-ISO-plate.kicad_sch (2023-04-24)

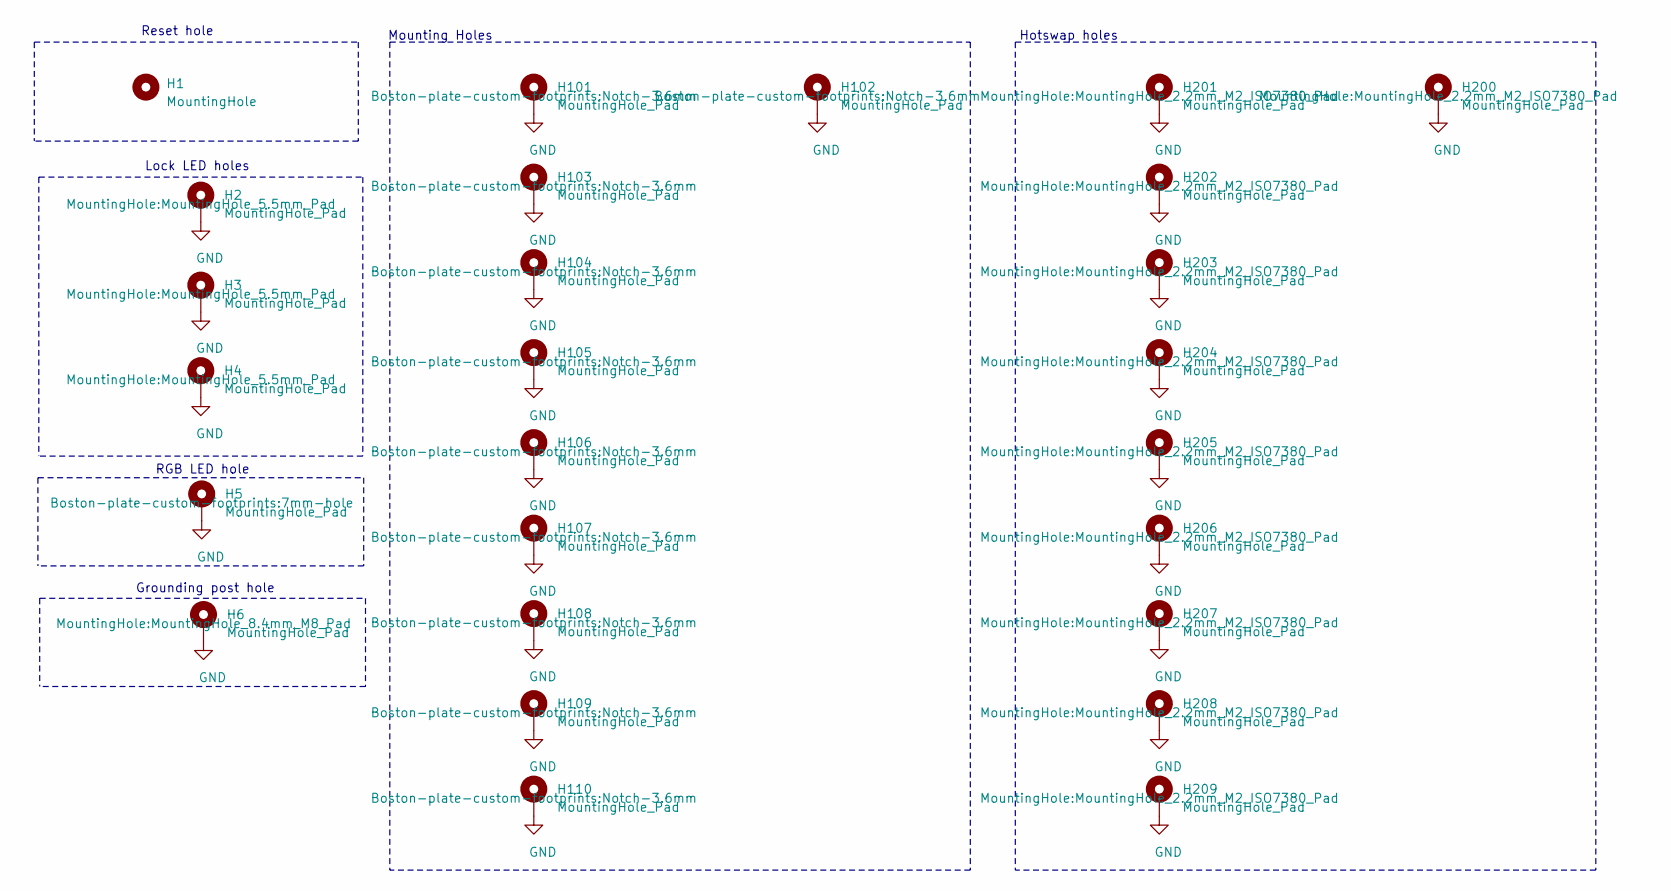
[picture p195: schematic FR4-hotswap-ISO-plate.kicad_sch]

Parts:
H1: MountingHole; 6x6-Tact-switch-opening-enlarged
H2, H3, H4: MountingHole_Pad; MountingHole_5.5mm_Pad
H5: MountingHole_Pad; 7mm-hole
H6: MountingHole_Pad; MountingHole_8.4mm_M8_Pad
H101, H102, H103, H104, H105, H106, H107, H108, H109, H110: MountingHole_Pad; Notch-3.6mm
H200, H201, H202, H203, H204, H205, H206, H207, H208, H209: MountingHole_Pad; MountingHole_2.2mm_M2_ISO7380_Pad

Connections:
GND: H2.1, H3.1, H4.1, H5.1, H6.1, H101.1, H102.1, H103.1, H104.1, H105.1, H106.1, H107.1, H108.1, H109.1, H110.1, H200.1, H201.1, H202.1, H203.1, H204.1, H205.1, H206.1, H207.1, H208.1, H209.1

Notes on the sheet:
RGB LED hole
Reset hole
Mounting Holes
Hotswap holes
Grounding post hole
Lock LED holes
