bluepylons/Boston/Boston - Current design/CNC version/Plate/Soldered-ANSI-fixed-layout/KiCAD files/Boston-CNC-soldered-ANSI-plate-FR4.kicad_sch

## KiCad design Boston - Current design/CNC version/Plate/Soldered-ANSI-fixed-layout/KiCAD files/Boston-CNC-soldered-ANSI-plate-FR4.kicad_sch (2023-04-24)

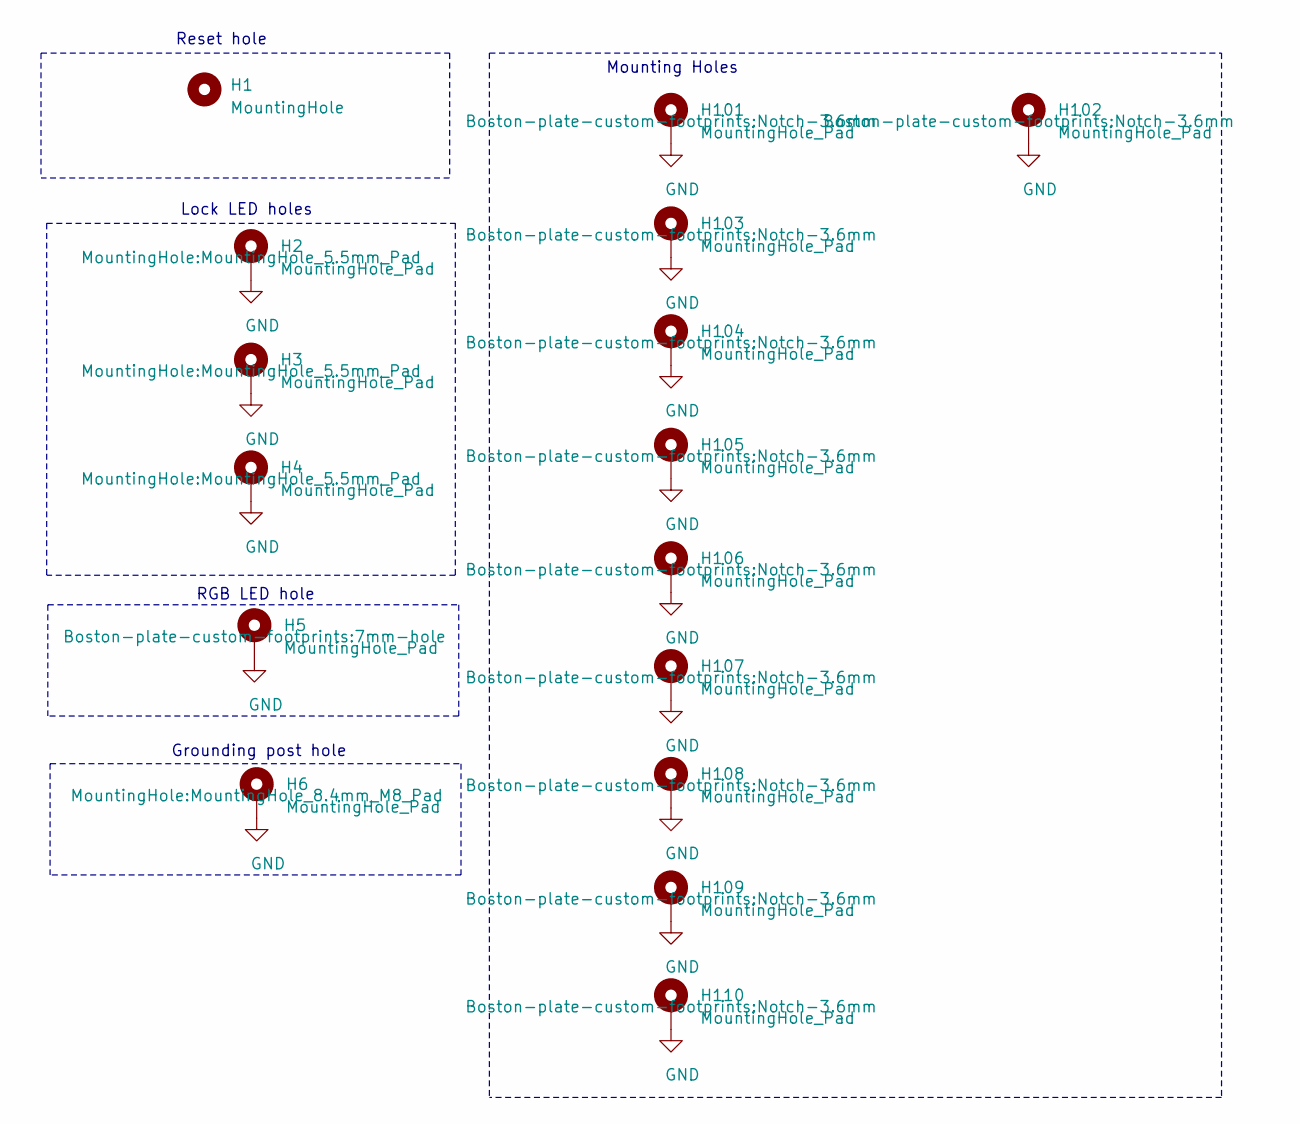
[picture p196: schematic Boston-CNC-soldered-ANSI-plate-FR4.kicad_sch]

Parts:
H1: MountingHole; 6x6-Tact-switch-opening
H2, H3, H4: MountingHole_Pad; MountingHole_5.5mm_Pad
H5: MountingHole_Pad; 7mm-hole
H6: MountingHole_Pad; MountingHole_8.4mm_M8_Pad
H101, H102, H103, H104, H105, H106, H107, H108, H109, H110: MountingHole_Pad; Notch-3.6mm

Connections:
GND: H2.1, H3.1, H4.1, H5.1, H6.1, H101.1, H102.1, H103.1, H104.1, H105.1, H106.1, H107.1, H108.1, H109.1, H110.1

Notes on the sheet:
Reset hole
Lock LED holes
RGB LED hole
Grounding post hole
Mounting Holes
