bluepylons/Boston/Boston - Current design/PCB/V0.8.2DHA/Boston-keyboard-V082DHA.kicad_sch

## KiCad design Boston - Current design/PCB/V0.8.2DHA/Boston-keyboard-V082DHA.kicad_sch (2023-06-07)

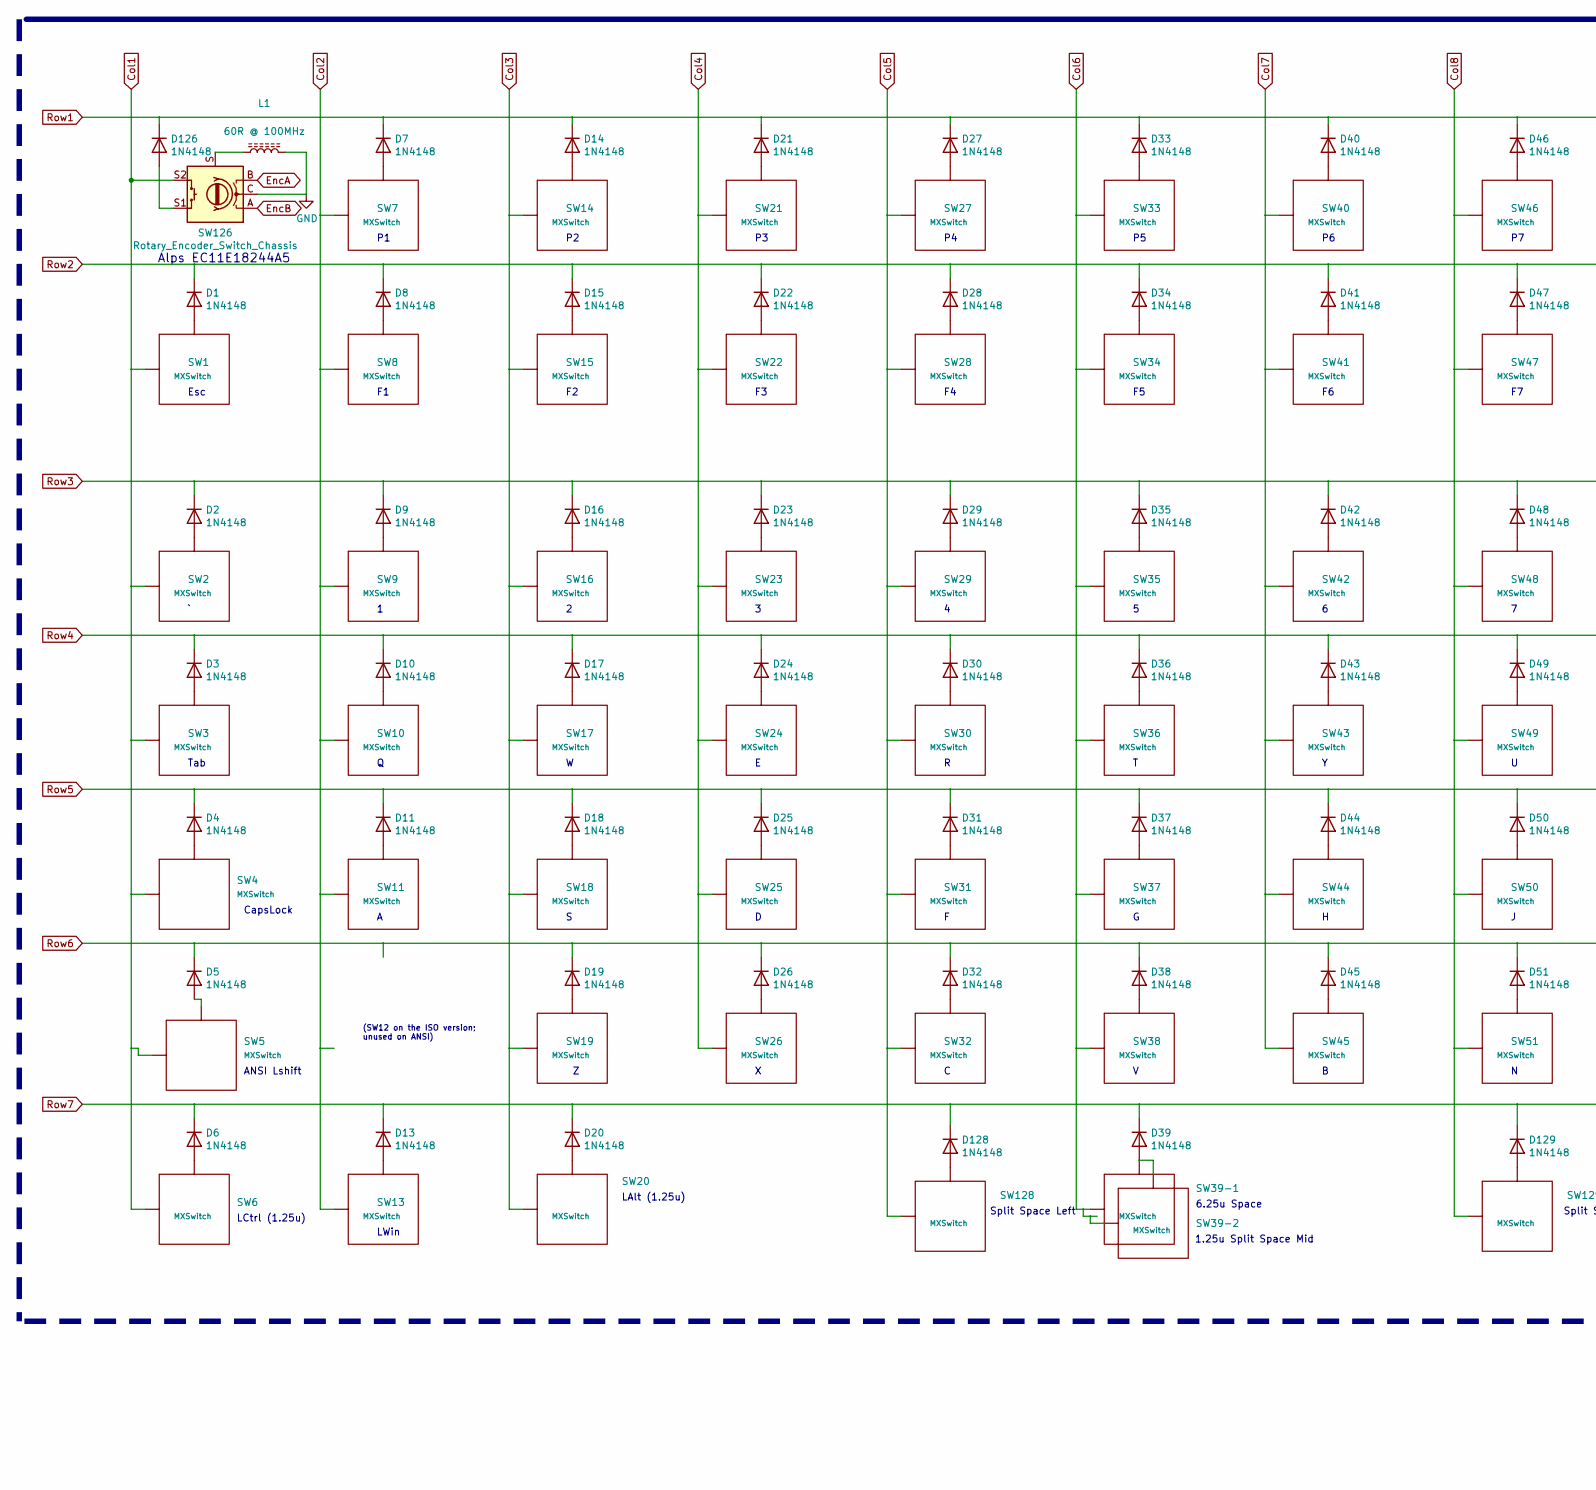
[picture p203: schematic Boston-keyboard-V082DHA.kicad_sch, part in row 1, column 1]

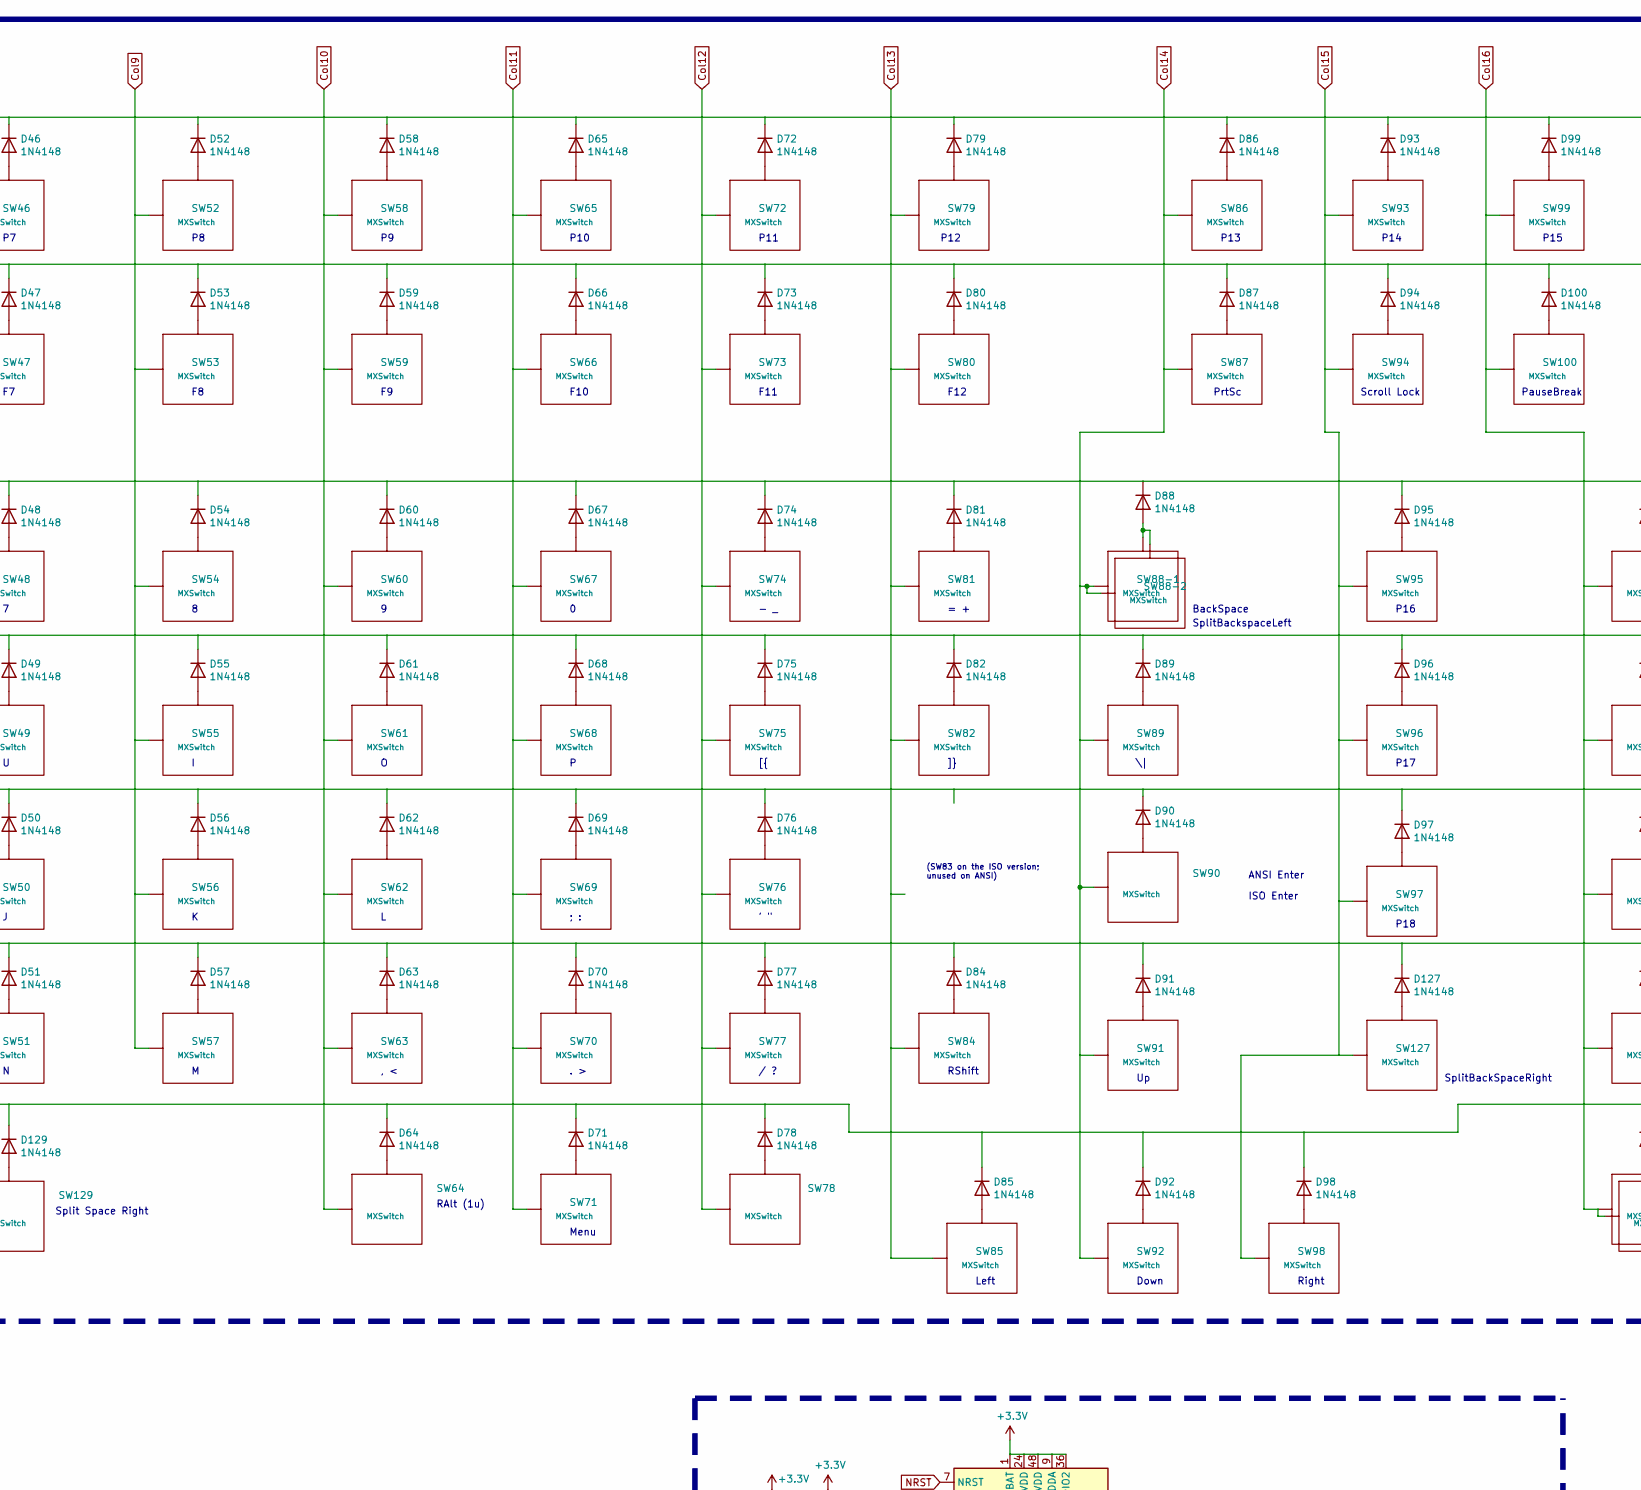
[picture p204: schematic Boston-keyboard-V082DHA.kicad_sch, part in row 1, column 2]

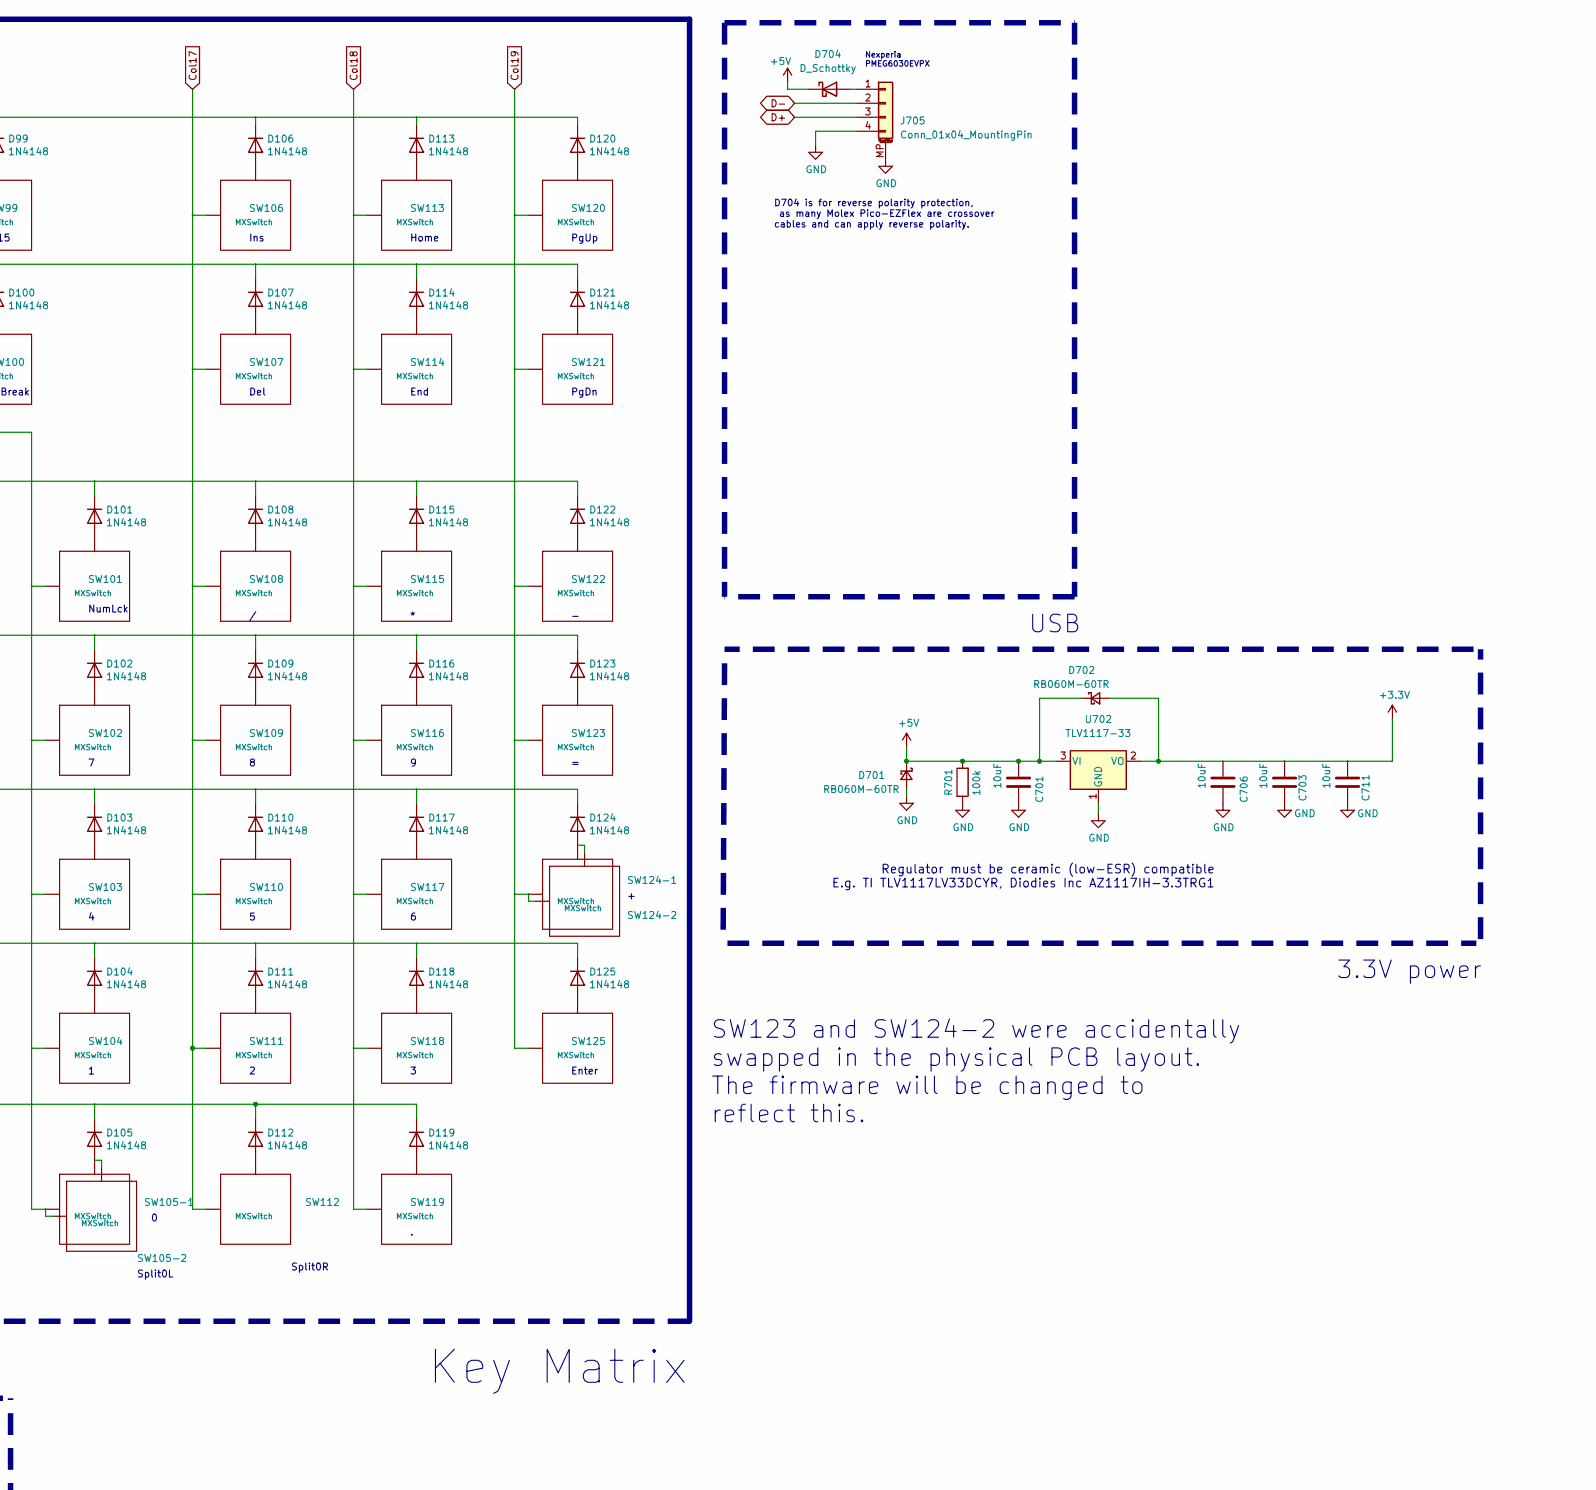
[picture p205: schematic Boston-keyboard-V082DHA.kicad_sch, part in row 1, column 3]

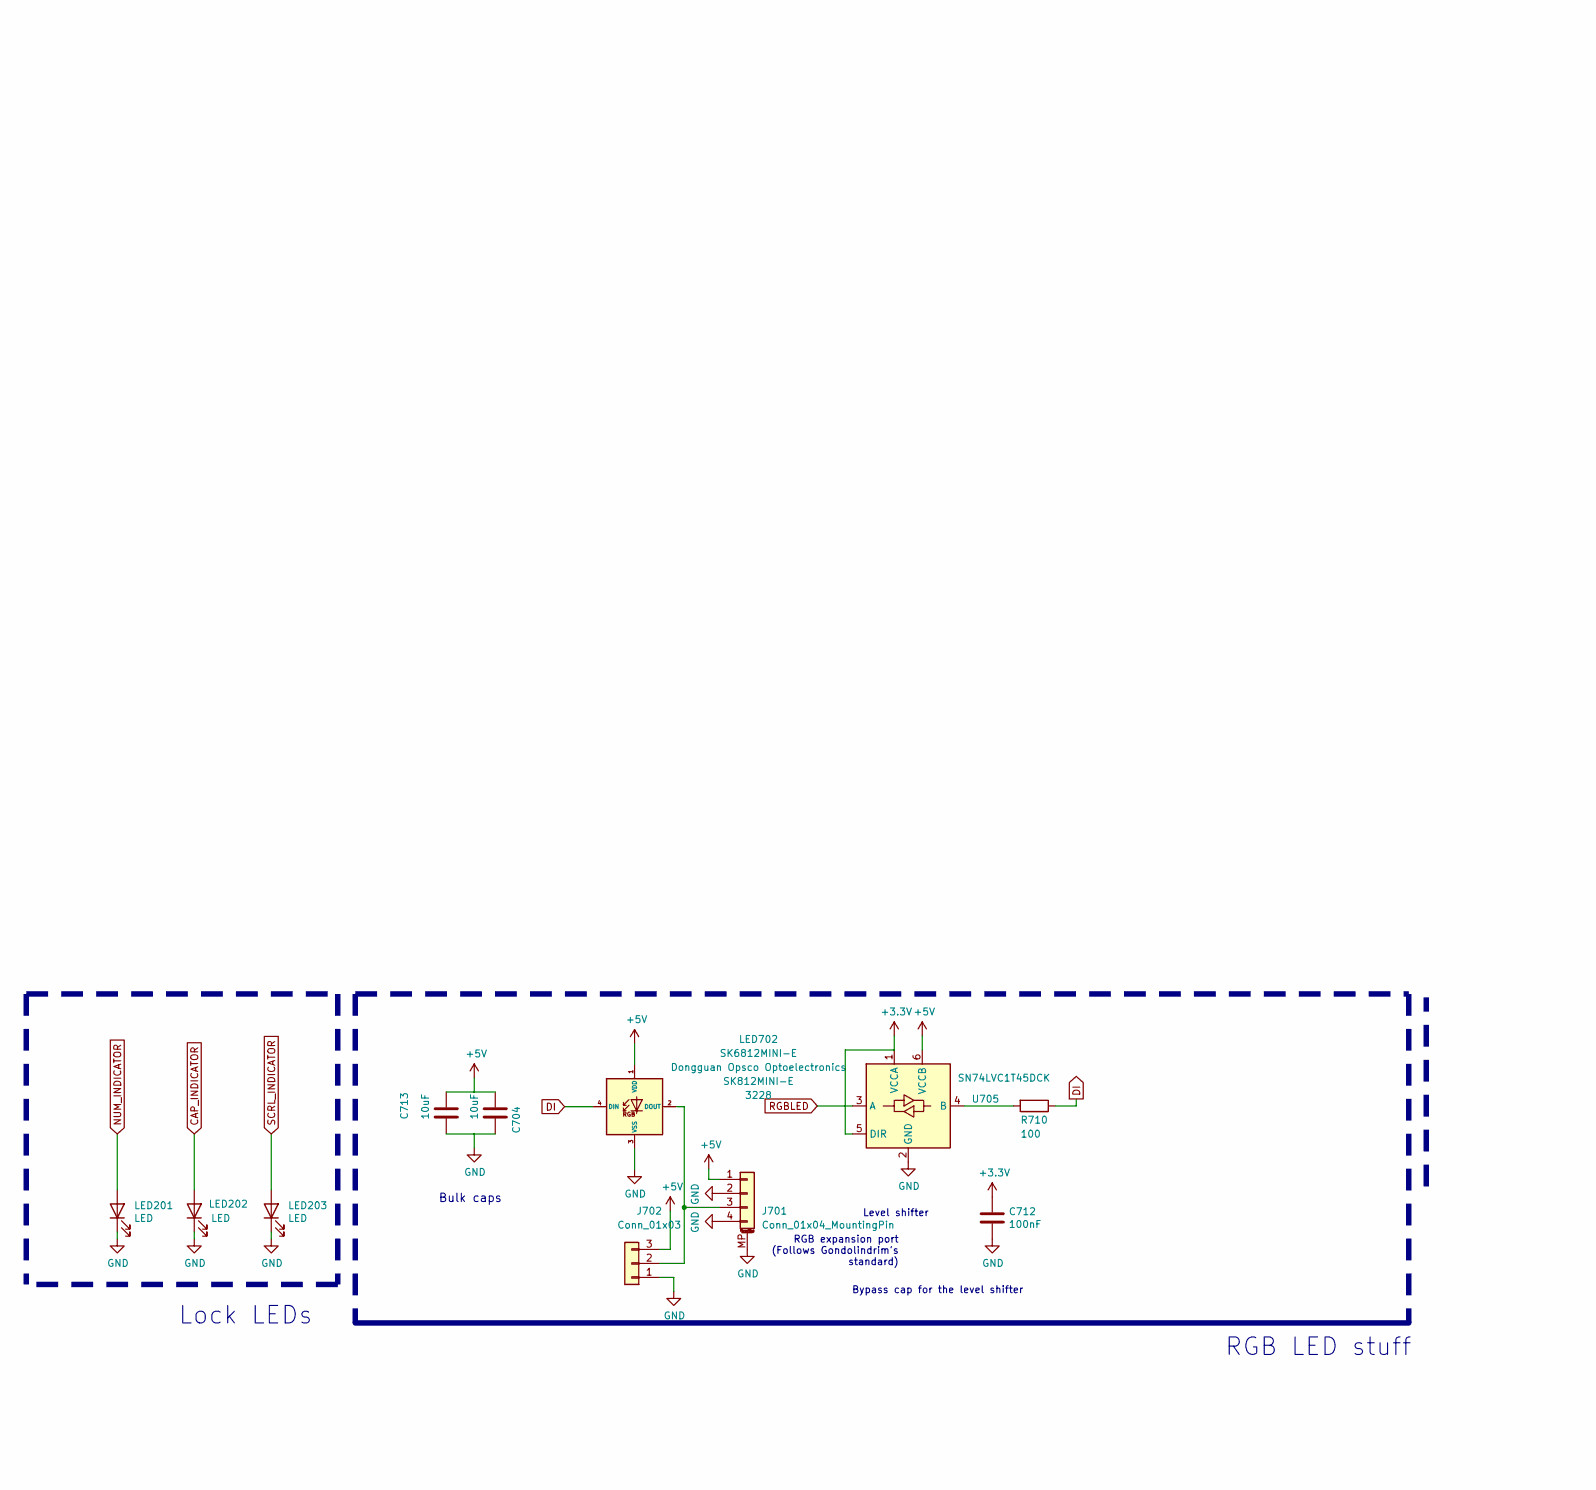
[picture p206: schematic Boston-keyboard-V082DHA.kicad_sch, part in row 2, column 1]

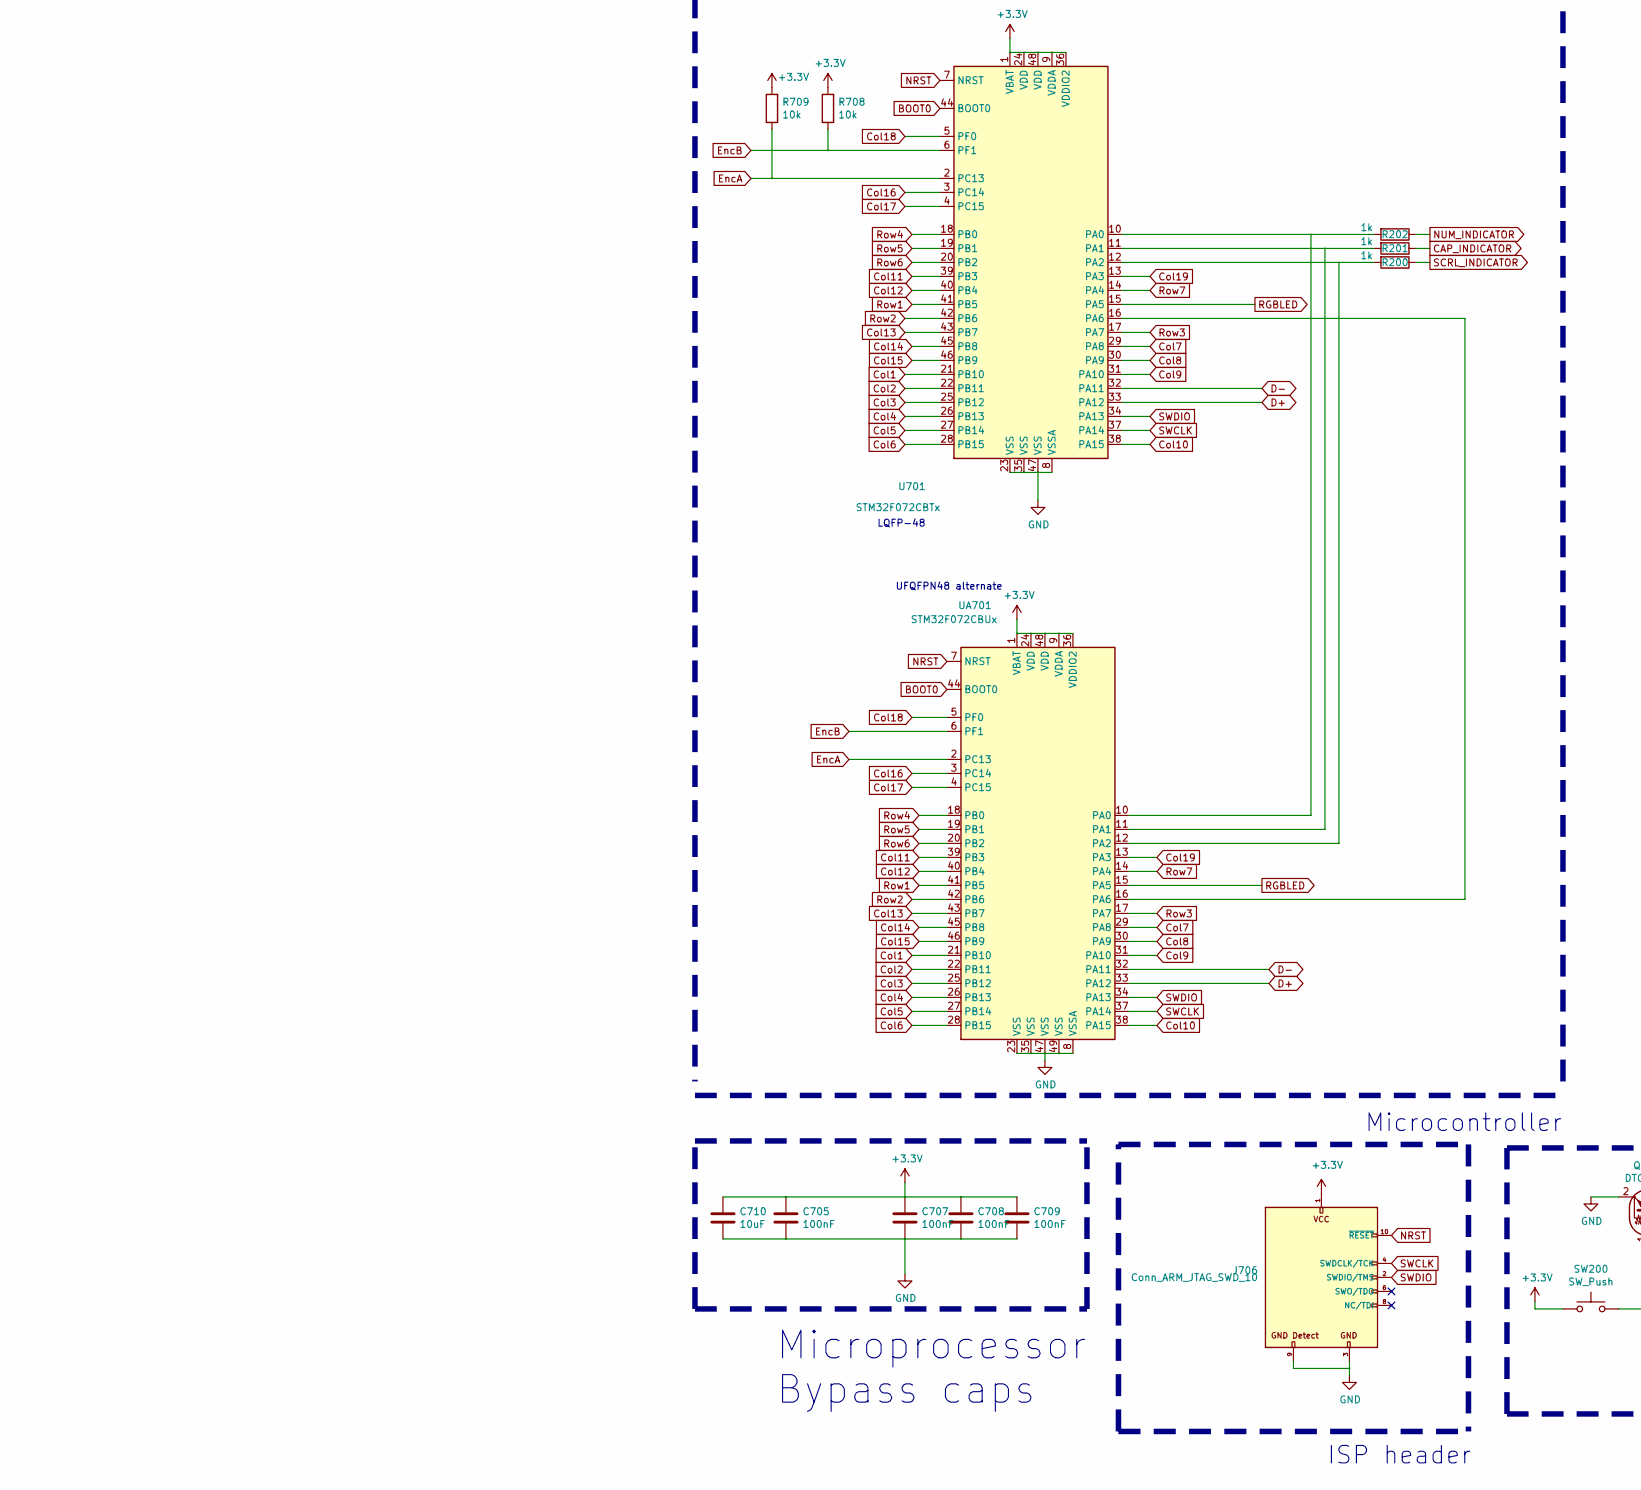
[picture p207: schematic Boston-keyboard-V082DHA.kicad_sch, part in row 2, column 2]

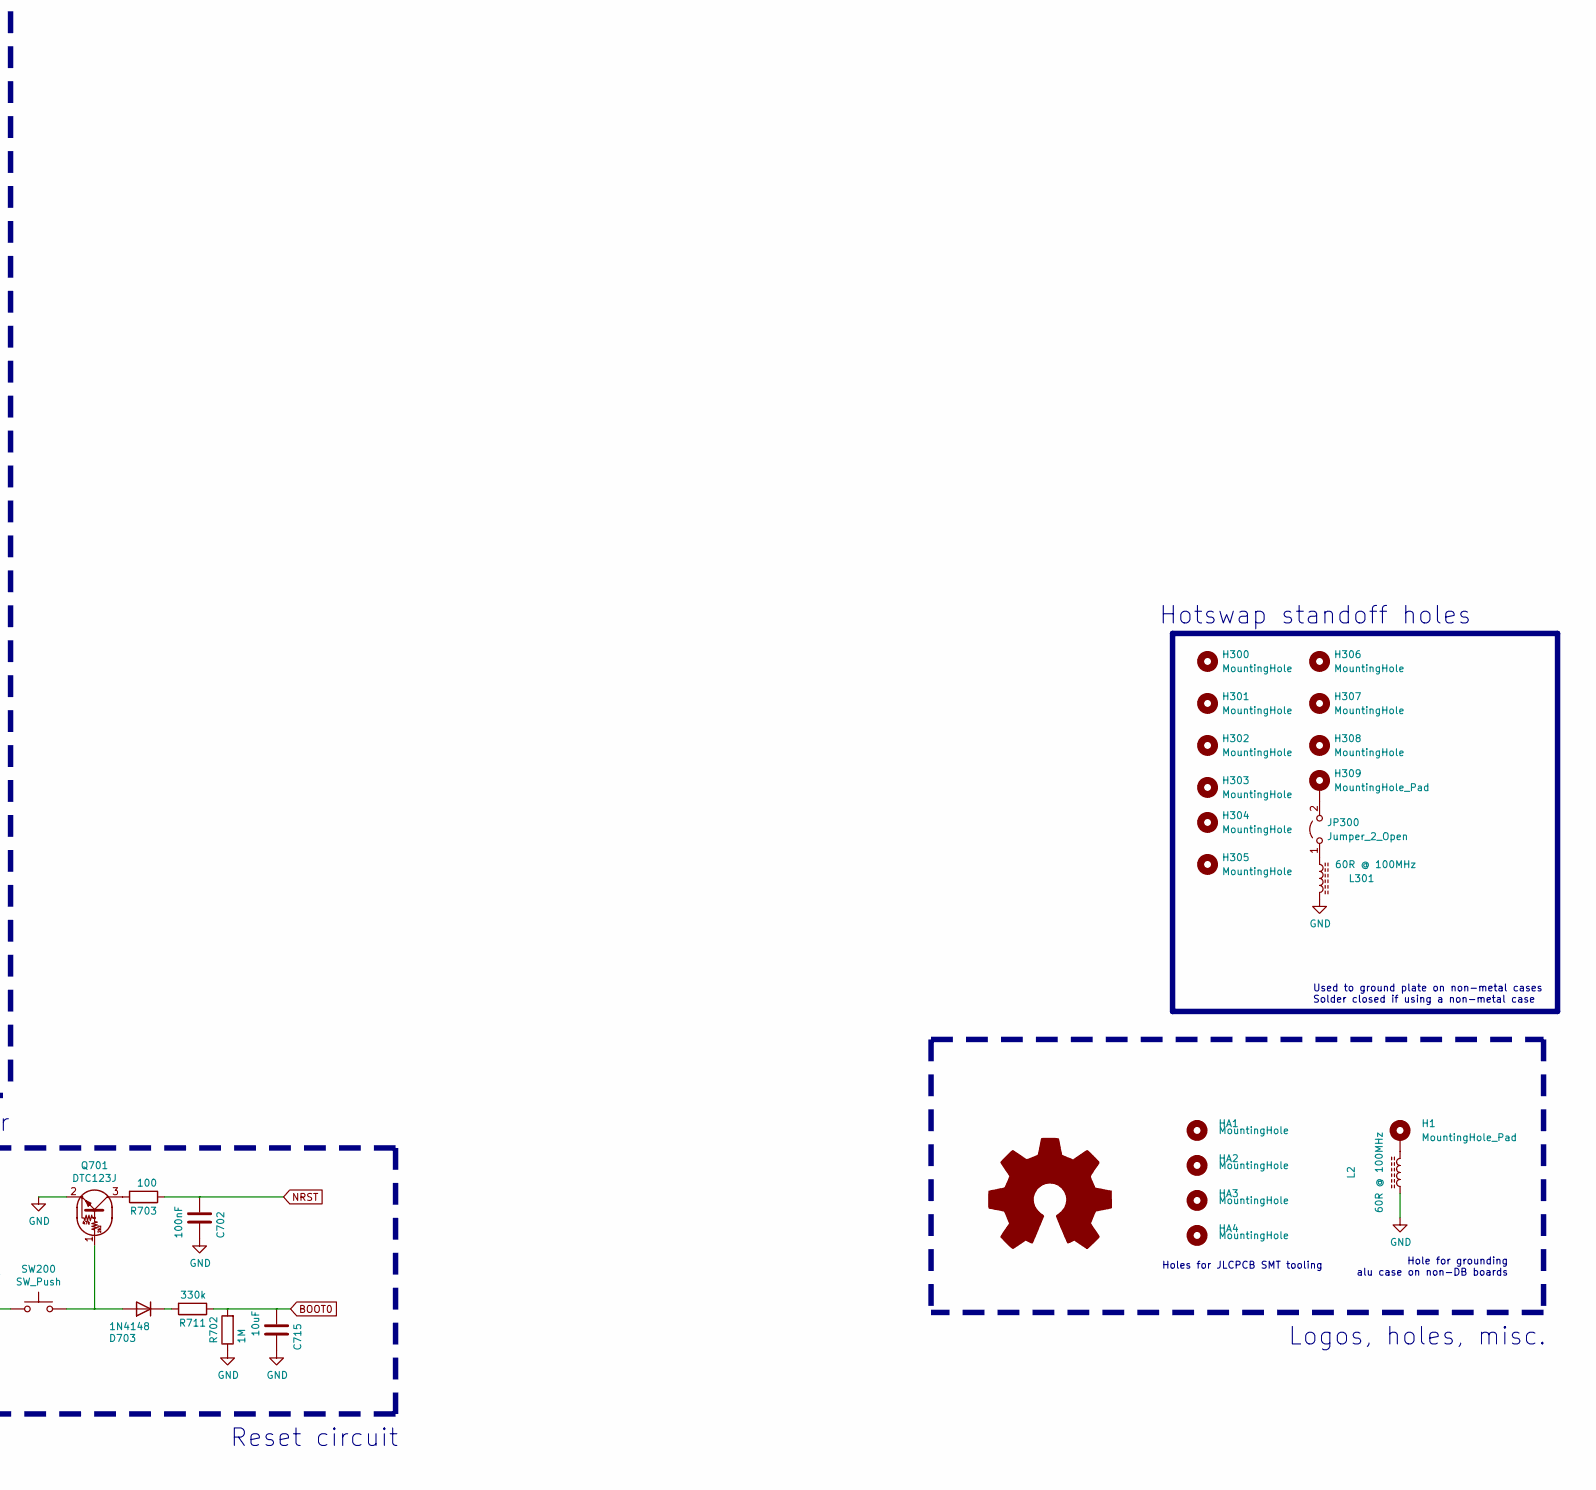
[picture p208: schematic Boston-keyboard-V082DHA.kicad_sch, part in row 2, column 3]

Parts:
C701, C703, C704, C706, C710, C711, C713, C715: 10uF; C_1206_3216Metric_Pad1.42x1.75mm_HandSolder
C702, C705, C707, C708, C709, C712: 100nF; C_0805_2012Metric_Pad1.15x1.40mm_HandSolder
D1, D2, D3, D4, D5, D6, D7, D8, D9, D10, D11, D13, D14, D15, D16, D17, D18, D19, D20, D21, D22, D23, D24, D25, D26, D27, D28, D29, D30, D31, D32, D33, D34, D35, D36, D37, D38, D39, D40, D41, D42, D43, D44, D45, D46, D47, D48, D49, D50, D51, D52, D53, D54, D55, D56, D57, D58, D59, D60, D61, D62, D63, D64, D65, D66, D67, D68, D69, D70, D71, D72, D73, D74, D75, D76, D77, D78, D79, D80, D81, D82, D84, D85, D86, D87, D88, D89, D90, D91, D92, D93, D94, D95, D96, D97, D98, D99, D100, D101, D102, D103, D104, D105, D106, D107, D108, D109, D110, D111, D112, D113, D114, D115, D116, D117, D118, D119, D120, D121, D122, D123, D124, D125, D126, D127, D128, D129, D703: 1N4148; D_SOD-123
D701, D702: RB060M-60TR; D_SOD-123
D704: D_Schottky; D_SOD-128
H1: MountingHole_Pad; MountingHole_3.5mm_Pad_Via
H300, H301, H302, H303, H304, H305, H306, H307, H308: MountingHole; MountingHole_2.2mm_M2_ISO7380
H309: MountingHole_Pad; MountingHole_2.2mm_M2_ISO7380_Pad
HA1, HA2, HA3, HA4: MountingHole; ToolingHole_1.152mm_(for_JLCPCB_SMT)
J701: Conn_01x04_MountingPin; SM04B-SRSS-TB(LF)(SN)_mounting-reliefs
J702: Conn_01x03; PinSocket_1x03_P2.54mm_Vertical
J705: Conn_01x04_MountingPin; Molex_Pico-EZmate_78171-0004_1x04-1MP_P1.20mm_Vertical
J706: Conn_ARM_JTAG_SWD_10; PinSocket_2x05_P2.54mm_Vertical
JP300: Jumper_2_Open; SolderJumper-2_P1.3mm_Open_TrianglePad1.0x1.5mm
L1, L2, L301: 60R @ 100MHz; L_0805_2012Metric_Pad1.15x1.40mm_HandSolder
LED201, LED202, LED203: LED; LED_D3.0mm_Clear
LED702: SK6812MINI-E; SK6812MINI_3535_6028_3.2x2.8mm_Round; MPN SK812MINI-E
LOGO2: Logo_Open_Hardware_Large; OSHW-Logo_11.4x12mm_SilkScreen
Q701: DTC123J; SOT-23
R200, R201, R202: 1k; R_0805_2012Metric_Pad1.20x1.40mm_HandSolder
R701: 100k; R_0805_2012Metric_Pad1.20x1.40mm_HandSolder
R702: 1M; R_0805_2012Metric_Pad1.15x1.40mm_HandSolder
R703, R710: 100; R_0805_2012Metric_Pad1.15x1.40mm_HandSolder
R708, R709: 10k; R_0805_2012Metric_Pad1.15x1.40mm_HandSolder
R711: 330k; R_0805_2012Metric_Pad1.15x1.40mm_HandSolder
SW1, SW2, SW7, SW8, SW9, SW10, SW11, SW14, SW15, SW16, SW17, SW18, SW19, SW21, SW22, SW23, SW24, SW25, SW26, SW27, SW28, SW29, SW30, SW31, SW32, SW33, SW34, SW35, SW36, SW37, SW38, SW40, SW41, SW42, SW43, SW44, SW45, SW46, SW47, SW48, SW49, SW50, SW51, SW52, SW53, SW54, SW55, SW56, SW57, SW58, SW59, SW60, SW61, SW62, SW63, SW64, SW65, SW66, SW67, SW68, SW69, SW70, SW71, SW72, SW73, SW74, SW75, SW76, SW77, SW78, SW79, SW80, SW81, SW82, SW85, SW86, SW87, SW88-2, SW91, SW92, SW93, SW94, SW95, SW96, SW97, SW98, SW99, SW100, SW101, SW102, SW103, SW104, SW105-2, SW106, SW107, SW108, SW109, SW110, SW111, SW112, SW113, SW114, SW115, SW116, SW117, SW118, SW119, SW120, SW121, SW122, SW123, SW124-2, SW127: MXSwitch; MX100H
SW3, SW89: MXSwitch; MX150H
SW4, SW84: MXSwitch; MX175H
SW5, SW90, SW129: MXSwitch; MX225H
SW6, SW13, SW20, SW39-2: MXSwitch; MX125H
SW39-1: MXSwitch; MX625H
SW88-1, SW105-1, SW124-1: MXSwitch; MX200H
SW125: MXSwitch; MX200HR
SW126: Rotary_Encoder_Switch_Chassis; ALPS_EC11E
SW128: MXSwitch; MX275H
SW200: SW_Push; SW_PUSH_6mm_H5mm
U701: STM32F072CBTx; LQFP-48_7x7mm_P0.5mm
U702: TLV1117-33; SOT-223-3_TabPin2
U705: SN74LVC1T45DCK; SOT-23-6_Handsoldering
UA701: STM32F072CBUx; QFN-48-1EP_7x7mm_P0.5mm_EP5.6x5.6mm

Connections:
+3.3V: C703.1, C705.1, C706.1, C707.1, C708.1, C709.1, C710.1, C711.1, C712.1, D702.2 (A), J706.1 (VCC), R708.2, R709.2, SW200.1, U701.1 (VBAT), U701.9 (VDDA), U701.24 (VDD), U701.36 (VDDIO2), U701.48 (VDD), U702.2 (VO), U705.1 (VCCA), U705.5 (DIR), UA701.1 (VBAT), UA701.9 (VDDA), UA701.24 (VDD), UA701.36 (VDDIO2), UA701.48 (VDD)
+5V: C701.1, C704.1, C713.1, D701.1 (K), D702.1 (K), D704.1 (K), J701.1, J702.3, LED702.1 (VDD), R701.2, U702.3 (VI), U705.6 (VCCB)
BOOT0: C715.1, R702.2, R711.1, U701.44 (BOOT0), UA701.44 (BOOT0)
CAP_INDICATOR: LED202.2 (A), R201.1
Col1: SW1.1 (Col), SW2.1 (Col), SW3.1 (Col), SW4.1 (Col), SW5.1 (Col), SW6.1 (Col), SW126.S2, U701.21 (PB10), UA701.21 (PB10)
Col2: SW7.1 (Col), SW8.1 (Col), SW9.1 (Col), SW10.1 (Col), SW11.1 (Col), SW13.1 (Col), U701.22 (PB11), UA701.22 (PB11)
Col3: SW14.1 (Col), SW15.1 (Col), SW16.1 (Col), SW17.1 (Col), SW18.1 (Col), SW19.1 (Col), SW20.1 (Col), U701.25 (PB12), UA701.25 (PB12)
Col4: SW21.1 (Col), SW22.1 (Col), SW23.1 (Col), SW24.1 (Col), SW25.1 (Col), SW26.1 (Col), U701.26 (PB13), UA701.26 (PB13)
Col5: SW27.1 (Col), SW28.1 (Col), SW29.1 (Col), SW30.1 (Col), SW31.1 (Col), SW32.1 (Col), SW128.1 (Col), U701.27 (PB14), UA701.27 (PB14)
Col6: SW33.1 (Col), SW34.1 (Col), SW35.1 (Col), SW36.1 (Col), SW37.1 (Col), SW38.1 (Col), SW39-1.1 (Col), SW39-2.1 (Col), U701.28 (PB15), UA701.28 (PB15)
Col7: SW40.1 (Col), SW41.1 (Col), SW42.1 (Col), SW43.1 (Col), SW44.1 (Col), SW45.1 (Col), U701.29 (PA8), UA701.29 (PA8)
Col8: SW46.1 (Col), SW47.1 (Col), SW48.1 (Col), SW49.1 (Col), SW50.1 (Col), SW51.1 (Col), SW129.1 (Col), U701.30 (PA9), UA701.30 (PA9)
Col9: SW52.1 (Col), SW53.1 (Col), SW54.1 (Col), SW55.1 (Col), SW56.1 (Col), SW57.1 (Col), U701.31 (PA10), UA701.31 (PA10)
Col10: SW58.1 (Col), SW59.1 (Col), SW60.1 (Col), SW61.1 (Col), SW62.1 (Col), SW63.1 (Col), SW64.1 (Col), U701.38 (PA15), UA701.38 (PA15)
Col11: SW65.1 (Col), SW66.1 (Col), SW67.1 (Col), SW68.1 (Col), SW69.1 (Col), SW70.1 (Col), SW71.1 (Col), U701.39 (PB3), UA701.39 (PB3)
Col12: SW72.1 (Col), SW73.1 (Col), SW74.1 (Col), SW75.1 (Col), SW76.1 (Col), SW77.1 (Col), SW78.1 (Col), U701.40 (PB4), UA701.40 (PB4)
Col13: SW79.1 (Col), SW80.1 (Col), SW81.1 (Col), SW82.1 (Col), SW84.1 (Col), SW85.1 (Col), U701.43 (PB7), UA701.43 (PB7)
Col14: SW86.1 (Col), SW87.1 (Col), SW88-1.1 (Col), SW88-2.1 (Col), SW89.1 (Col), SW90.1 (Col), SW91.1 (Col), SW92.1 (Col), U701.45 (PB8), UA701.45 (PB8)
Col15: SW93.1 (Col), SW94.1 (Col), SW95.1 (Col), SW96.1 (Col), SW97.1 (Col), SW98.1 (Col), SW127.1 (Col), U701.46 (PB9), UA701.46 (PB9)
Col16: SW99.1 (Col), SW100.1 (Col), SW101.1 (Col), SW102.1 (Col), SW103.1 (Col), SW104.1 (Col), SW105-1.1 (Col), SW105-2.1 (Col), U701.3 (PC14), UA701.3 (PC14)
Col17: SW106.1 (Col), SW107.1 (Col), SW108.1 (Col), SW109.1 (Col), SW110.1 (Col), SW111.1 (Col), SW112.1 (Col), U701.4 (PC15), UA701.4 (PC15)
Col18: SW113.1 (Col), SW114.1 (Col), SW115.1 (Col), SW116.1 (Col), SW117.1 (Col), SW118.1 (Col), SW119.1 (Col), U701.5 (PF0), UA701.5 (PF0)
Col19: SW120.1 (Col), SW121.1 (Col), SW122.1 (Col), SW123.1 (Col), SW124-1.1 (Col), SW124-2.1 (Col), SW125.1 (Col), U701.13 (PA3), UA701.13 (PA3)
D+: J705.3, U701.33 (PA12), UA701.33 (PA12)
D-: J705.2, U701.32 (PA11), UA701.32 (PA11)
DI: LED702.4 (DIN), R710.1
EncA: R709.1, SW126.B, U701.2 (PC13), UA701.2 (PC13)
EncB: R708.1, SW126.A, U701.6 (PF1), UA701.6 (PF1)
GND: C701.2, C702.2, C703.2, C704.2, C705.2, C706.2, C707.2, C708.2, C709.2, C710.2, C711.2, C712.2, C713.2, C715.2, D701.2 (A), J701.2, J701.4, J701.MP (MountPin), J702.1, J705.4, J705.MP (MountPin), J706.3 (GND), J706.5 (GND), J706.9 (GNDDetect), L1.2, L2.1, L301.2, LED201.1 (K), LED202.1 (K), LED203.1 (K), LED702.3 (VSS), Q701.2 (E), R701.1, R702.1, SW126.C, U701.8 (VSSA), U701.23 (VSS), U701.35 (VSS), U701.47 (VSS), U702.1 (GND), U705.2 (GND), UA701.8 (VSSA), UA701.23 (VSS), UA701.35 (VSS), UA701.47 (VSS), UA701.49 (VSS)
NRST: C702.1, J706.10 (~RESET), R703.1, U701.7 (NRST), UA701.7 (NRST)
NUM_INDICATOR: LED201.2 (A), R202.1
unnamed: D1.2 (A), SW1.2 (Row)
unnamed: D2.2 (A), SW2.2 (Row)
unnamed: D3.2 (A), SW3.2 (Row)
unnamed: D4.2 (A), SW4.2 (Row)
unnamed: D5.2 (A), SW5.2 (Row)
unnamed: D6.2 (A), SW6.2 (Row)
unnamed: D7.2 (A), SW7.2 (Row)
unnamed: D8.2 (A), SW8.2 (Row)
unnamed: D9.2 (A), SW9.2 (Row)
unnamed: D10.2 (A), SW10.2 (Row)
unnamed: D11.2 (A), SW11.2 (Row)
unnamed: D13.2 (A), SW13.2 (Row)
unnamed: D14.2 (A), SW14.2 (Row)
unnamed: D15.2 (A), SW15.2 (Row)
unnamed: D16.2 (A), SW16.2 (Row)
unnamed: D17.2 (A), SW17.2 (Row)
unnamed: D18.2 (A), SW18.2 (Row)
unnamed: D19.2 (A), SW19.2 (Row)
unnamed: D20.2 (A), SW20.2 (Row)
unnamed: D21.2 (A), SW21.2 (Row)
unnamed: D22.2 (A), SW22.2 (Row)
unnamed: D23.2 (A), SW23.2 (Row)
unnamed: D24.2 (A), SW24.2 (Row)
unnamed: D25.2 (A), SW25.2 (Row)
unnamed: D26.2 (A), SW26.2 (Row)
unnamed: D27.2 (A), SW27.2 (Row)
unnamed: D28.2 (A), SW28.2 (Row)
unnamed: D29.2 (A), SW29.2 (Row)
unnamed: D30.2 (A), SW30.2 (Row)
unnamed: D31.2 (A), SW31.2 (Row)
unnamed: D32.2 (A), SW32.2 (Row)
unnamed: D33.2 (A), SW33.2 (Row)
unnamed: D34.2 (A), SW34.2 (Row)
unnamed: D35.2 (A), SW35.2 (Row)
unnamed: D36.2 (A), SW36.2 (Row)
unnamed: D37.2 (A), SW37.2 (Row)
unnamed: D38.2 (A), SW38.2 (Row)
unnamed: D39.2 (A), SW39-1.2 (Row), SW39-2.2 (Row)
unnamed: D40.2 (A), SW40.2 (Row)
unnamed: D41.2 (A), SW41.2 (Row)
unnamed: D42.2 (A), SW42.2 (Row)
unnamed: D43.2 (A), SW43.2 (Row)
unnamed: D44.2 (A), SW44.2 (Row)
unnamed: D45.2 (A), SW45.2 (Row)
unnamed: D46.2 (A), SW46.2 (Row)
unnamed: D47.2 (A), SW47.2 (Row)
unnamed: D48.2 (A), SW48.2 (Row)
unnamed: D49.2 (A), SW49.2 (Row)
unnamed: D50.2 (A), SW50.2 (Row)
unnamed: D51.2 (A), SW51.2 (Row)
unnamed: D52.2 (A), SW52.2 (Row)
unnamed: D53.2 (A), SW53.2 (Row)
unnamed: D54.2 (A), SW54.2 (Row)
unnamed: D55.2 (A), SW55.2 (Row)
unnamed: D56.2 (A), SW56.2 (Row)
unnamed: D57.2 (A), SW57.2 (Row)
unnamed: D58.2 (A), SW58.2 (Row)
unnamed: D59.2 (A), SW59.2 (Row)
unnamed: D60.2 (A), SW60.2 (Row)
unnamed: D61.2 (A), SW61.2 (Row)
unnamed: D62.2 (A), SW62.2 (Row)
unnamed: D63.2 (A), SW63.2 (Row)
unnamed: D64.2 (A), SW64.2 (Row)
unnamed: D65.2 (A), SW65.2 (Row)
unnamed: D66.2 (A), SW66.2 (Row)
unnamed: D67.2 (A), SW67.2 (Row)
unnamed: D68.2 (A), SW68.2 (Row)
unnamed: D69.2 (A), SW69.2 (Row)
unnamed: D70.2 (A), SW70.2 (Row)
unnamed: D71.2 (A), SW71.2 (Row)
unnamed: D72.2 (A), SW72.2 (Row)
unnamed: D73.2 (A), SW73.2 (Row)
unnamed: D74.2 (A), SW74.2 (Row)
unnamed: D75.2 (A), SW75.2 (Row)
unnamed: D76.2 (A), SW76.2 (Row)
unnamed: D77.2 (A), SW77.2 (Row)
unnamed: D78.2 (A), SW78.2 (Row)
unnamed: D79.2 (A), SW79.2 (Row)
unnamed: D80.2 (A), SW80.2 (Row)
unnamed: D81.2 (A), SW81.2 (Row)
unnamed: D82.2 (A), SW82.2 (Row)
unnamed: D84.2 (A), SW84.2 (Row)
unnamed: D85.2 (A), SW85.2 (Row)
unnamed: D86.2 (A), SW86.2 (Row)
unnamed: D87.2 (A), SW87.2 (Row)
unnamed: D88.2 (A), SW88-1.2 (Row), SW88-2.2 (Row)
unnamed: D89.2 (A), SW89.2 (Row)
unnamed: D90.2 (A), SW90.2 (Row)
unnamed: D91.2 (A), SW91.2 (Row)
unnamed: D92.2 (A), SW92.2 (Row)
unnamed: D93.2 (A), SW93.2 (Row)
unnamed: D94.2 (A), SW94.2 (Row)
unnamed: D95.2 (A), SW95.2 (Row)
unnamed: D96.2 (A), SW96.2 (Row)
unnamed: D97.2 (A), SW97.2 (Row)
unnamed: D98.2 (A), SW98.2 (Row)
unnamed: D99.2 (A), SW99.2 (Row)
unnamed: D100.2 (A), SW100.2 (Row)
unnamed: D101.2 (A), SW101.2 (Row)
unnamed: D102.2 (A), SW102.2 (Row)
unnamed: D103.2 (A), SW103.2 (Row)
unnamed: D104.2 (A), SW104.2 (Row)
unnamed: D105.2 (A), SW105-1.2 (Row), SW105-2.2 (Row)
unnamed: D106.2 (A), SW106.2 (Row)
unnamed: D107.2 (A), SW107.2 (Row)
unnamed: D108.2 (A), SW108.2 (Row)
unnamed: D109.2 (A), SW109.2 (Row)
unnamed: D110.2 (A), SW110.2 (Row)
unnamed: D111.2 (A), SW111.2 (Row)
unnamed: D112.2 (A), SW112.2 (Row)
unnamed: D113.2 (A), SW113.2 (Row)
unnamed: D114.2 (A), SW114.2 (Row)
unnamed: D115.2 (A), SW115.2 (Row)
unnamed: D116.2 (A), SW116.2 (Row)
unnamed: D117.2 (A), SW117.2 (Row)
unnamed: D118.2 (A), SW118.2 (Row)
unnamed: D119.2 (A), SW119.2 (Row)
unnamed: D120.2 (A), SW120.2 (Row)
unnamed: D121.2 (A), SW121.2 (Row)
unnamed: D122.2 (A), SW122.2 (Row)
unnamed: D123.2 (A), SW123.2 (Row)
unnamed: D124.2 (A), SW124-1.2 (Row), SW124-2.2 (Row)
unnamed: D125.2 (A), SW125.2 (Row)
unnamed: D126.2 (A), SW126.S1
unnamed: D127.2 (A), SW127.2 (Row)
unnamed: D128.2 (A), SW128.2 (Row)
unnamed: D129.2 (A), SW129.2 (Row)
unnamed: D703.1 (K), R711.2
unnamed: D703.2 (A), Q701.1 (B), SW200.2
unnamed: D704.2 (A), J705.1
unnamed: H1.1, L2.2
unnamed: H309.1, JP300.2 (B)
unnamed: J701.3, J702.2, LED702.2 (DOUT)
unnamed: JP300.1 (A), L301.1
unnamed: L1.1, SW126.S (Shield)
unnamed: Q701.3 (C), R703.2
unnamed: R200.2, U701.12 (PA2), UA701.12 (PA2)
unnamed: R201.2, U701.11 (PA1), UA701.11 (PA1)
unnamed: R202.2, U701.10 (PA0), UA701.10 (PA0)
unnamed: R710.2, U705.4 (B)
unnamed: U701.16 (PA6), UA701.16 (PA6)
RGBLED: U701.15 (PA5), U705.3 (A), UA701.15 (PA5)
Row1: D7.1 (K), D14.1 (K), D21.1 (K), D27.1 (K), D33.1 (K), D40.1 (K), D46.1 (K), D52.1 (K), D58.1 (K), D65.1 (K), D72.1 (K), D79.1 (K), D86.1 (K), D93.1 (K), D99.1 (K), D106.1 (K), D113.1 (K), D120.1 (K), D126.1 (K), U701.41 (PB5), UA701.41 (PB5)
Row2: D1.1 (K), D8.1 (K), D15.1 (K), D22.1 (K), D28.1 (K), D34.1 (K), D41.1 (K), D47.1 (K), D53.1 (K), D59.1 (K), D66.1 (K), D73.1 (K), D80.1 (K), D87.1 (K), D94.1 (K), D100.1 (K), D107.1 (K), D114.1 (K), D121.1 (K), U701.42 (PB6), UA701.42 (PB6)
Row3: D2.1 (K), D9.1 (K), D16.1 (K), D23.1 (K), D29.1 (K), D35.1 (K), D42.1 (K), D48.1 (K), D54.1 (K), D60.1 (K), D67.1 (K), D74.1 (K), D81.1 (K), D88.1 (K), D95.1 (K), D101.1 (K), D108.1 (K), D115.1 (K), D122.1 (K), U701.17 (PA7), UA701.17 (PA7)
Row4: D3.1 (K), D10.1 (K), D17.1 (K), D24.1 (K), D30.1 (K), D36.1 (K), D43.1 (K), D49.1 (K), D55.1 (K), D61.1 (K), D68.1 (K), D75.1 (K), D82.1 (K), D89.1 (K), D96.1 (K), D102.1 (K), D109.1 (K), D116.1 (K), D123.1 (K), U701.18 (PB0), UA701.18 (PB0)
Row5: D4.1 (K), D11.1 (K), D18.1 (K), D25.1 (K), D31.1 (K), D37.1 (K), D44.1 (K), D50.1 (K), D56.1 (K), D62.1 (K), D69.1 (K), D76.1 (K), D90.1 (K), D97.1 (K), D103.1 (K), D110.1 (K), D117.1 (K), D124.1 (K), U701.19 (PB1), UA701.19 (PB1)
Row6: D5.1 (K), D19.1 (K), D26.1 (K), D32.1 (K), D38.1 (K), D45.1 (K), D51.1 (K), D57.1 (K), D63.1 (K), D70.1 (K), D77.1 (K), D84.1 (K), D91.1 (K), D104.1 (K), D111.1 (K), D118.1 (K), D125.1 (K), D127.1 (K), U701.20 (PB2), UA701.20 (PB2)
Row7: D6.1 (K), D13.1 (K), D20.1 (K), D39.1 (K), D64.1 (K), D71.1 (K), D78.1 (K), D85.1 (K), D92.1 (K), D98.1 (K), D105.1 (K), D112.1 (K), D119.1 (K), D128.1 (K), D129.1 (K), U701.14 (PA4), UA701.14 (PA4)
SCRL_INDICATOR: LED203.2 (A), R200.1
SWCLK: J706.4 (SWDCLK/TCK), U701.37 (PA14), UA701.37 (PA14)
SWDIO: J706.2 (SWDIO/TMS), U701.34 (PA13), UA701.34 (PA13)

Notes on the sheet:
; :
P18
/ ?
LWin
Enter
UFQFPN48 alternate
Used to ground plate on non-metal cases Solder closed if using a non-metal case
P11
3.3V power
P16
Hole for grounding alu case on non-DB boards
ISO Enter
Microcontroller
Nexperia PMEG6030EVPX
ANSI Lshift
SW123 and SW124-2 were accidentally swapped in the physical PCB layout. The firmware will be changed to reflect this.
. >
Split0R
`~{}
Split Space Left
Menu
NumLck
RGB expansion port (Follows Gondolindrim's standard)
RShift
Split Space Right
Home
Bypass cap for the level shifter
ANSI Enter
Logos, holes, misc.
(SW12 on the ISO version; unused on ANSI)
Down
SplitBackSpaceRight
RGB LED stuff
LAlt (1.25u)
PgUp
1.25u Split Space Mid
PgDn
ISP header
Regulator must be ceramic (low-ESR) compatible E.g. TI TLV1117LV33DCYR, Diodies Inc AZ1117IH-3.3TRG1
(SW83 on the ISO version; unused on ANSI)
SplitBackspaceLeft
BackSpace
P10
PrtSc
Right
Tab
Holes for JLCPCB SMT tooling
Alps EC11E18244A5
F11
LCtrl (1.25u)
RAlt (1u)
End
P15
- _
CapsLock
Scroll Lock
Level shifter
6.25u Space
Hotswap standoff holes
Split0L
PauseBreak
USB
D704 is for reverse polarity protection, as many Molex Pico-EZFlex are crossover cables and can apply reverse polarity.
P14
Ins
Del
Key Matrix
Lock LEDs
, <
' "
Reset circuit
P12
LQFP-48
P17
= +
F12
P13
Left
F10
Bulk caps
Esc
Microprocessor Bypass caps
