bluepylons/Boston/Boston - Current design/3D printed version/Bottom (without reset hole)/KiCAD files/bottom-no-hole.kicad_sch

## KiCad design Boston - Current design/3D printed version/Bottom (without reset hole)/KiCAD files/bottom-no-hole.kicad_sch (2023-04-24)

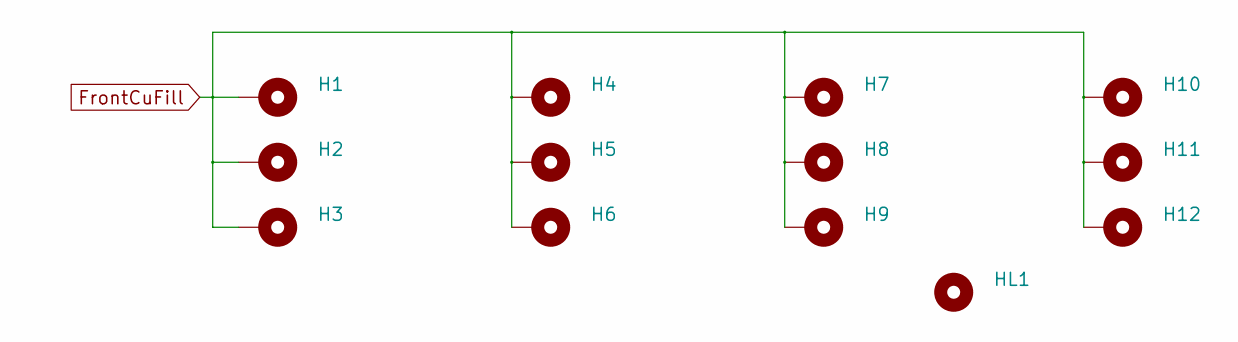
[picture p209: schematic bottom-no-hole.kicad_sch]

Parts:
H1, H2, H3, H4, H5, H6, H7, H8, H9, H10, H11, H12: (no value)
HL1: (no value)

Connections:
FrontCuFill: H1.1, H2.1, H3.1, H4.1, H5.1, H6.1, H7.1, H8.1, H9.1, H10.1, H11.1, H12.1
